hybrid-lab/PyOpticL_Rubidium_System/Production/Repumper_consolidated/Repumper_consolidated2.png

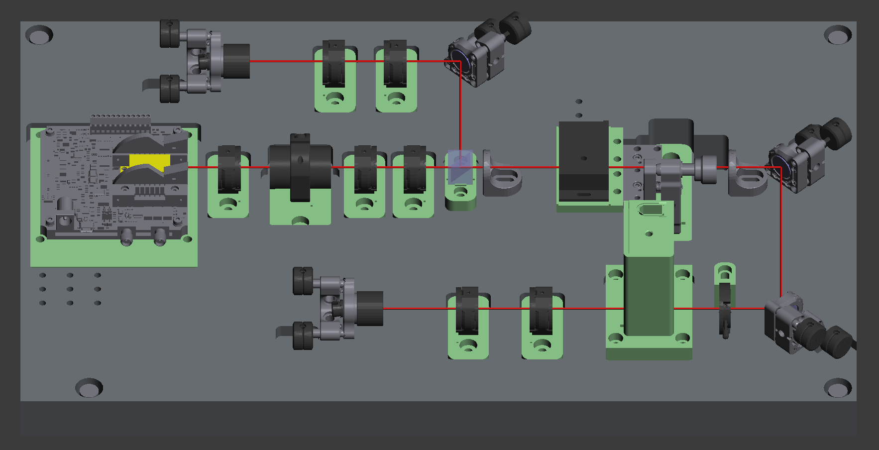
Production/Repumper_consolidated/Repumper_consolidated2.png
