hybrid-lab/PyOpticL_Rubidium_System/Rubidium_system/3DModel/StepFiles_unsorted/IsolatorSurfaceAdaptor.step

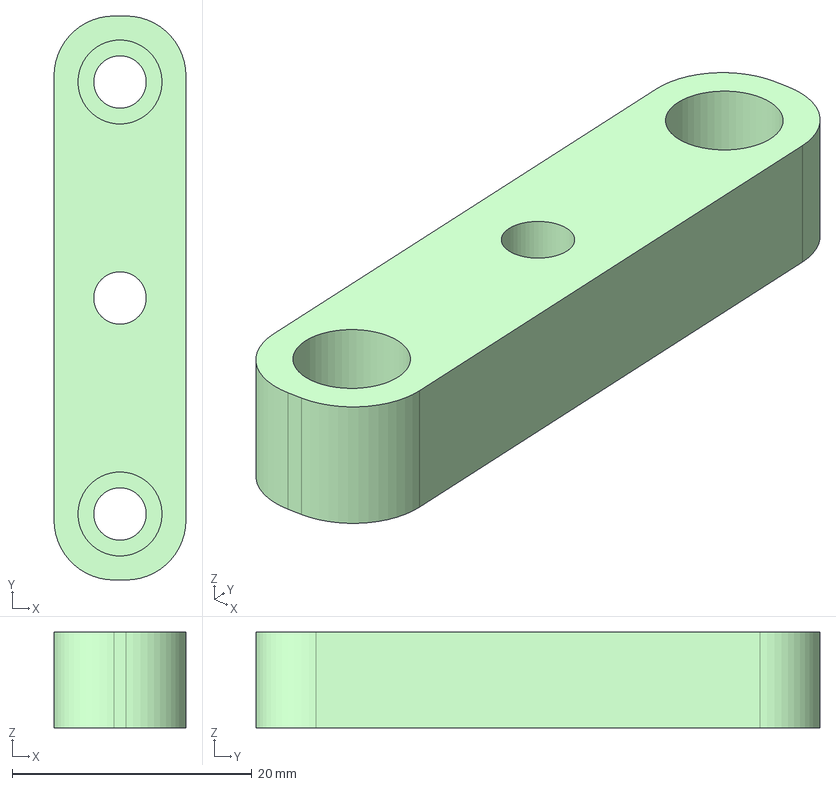
[picture p30: CAD file, 2025-08-15]
Rubidium_system/3DModel/StepFiles_unsorted/IsolatorSurfaceAdaptor.step
11.0 x 47.0 x 8.00 mm
