hybrid-lab/PyOpticL_Rubidium_System/stl/JosiahExportedSTLs/eyP-BFW01-171218.stl

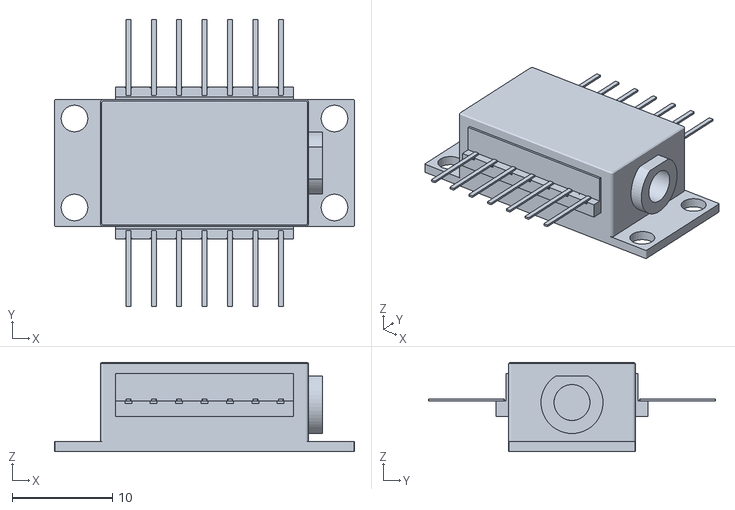
[picture p31: CAD file, 2025-08-15]
stl/JosiahExportedSTLs/eyP-BFW01-171218.stl
30.0 x 28.7 x 8.90
