hybrid-lab/PyOpticL_Rubidium_System/stl/KA05A.stl

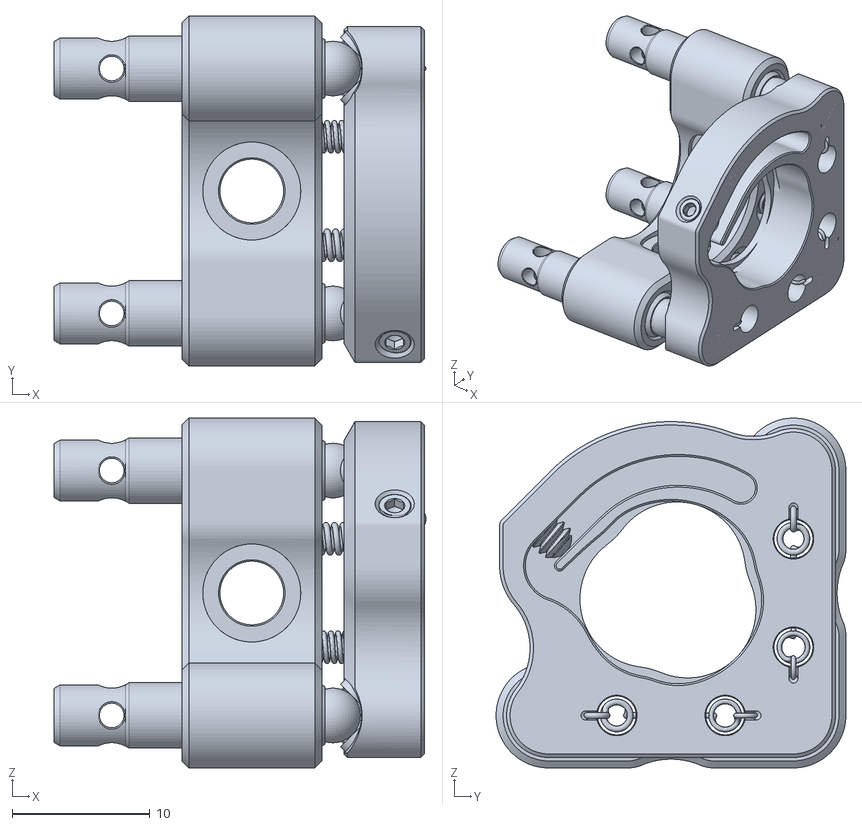
[picture p32: CAD file, 2026-06-10]
stl/KA05A.stl
27.0 x 25.4 x 25.4
