hybrid-lab/PyOpticL_Rubidium_System/stl/Shared-PyOpticL-Folder/POLARIS-B1G-Step.stl

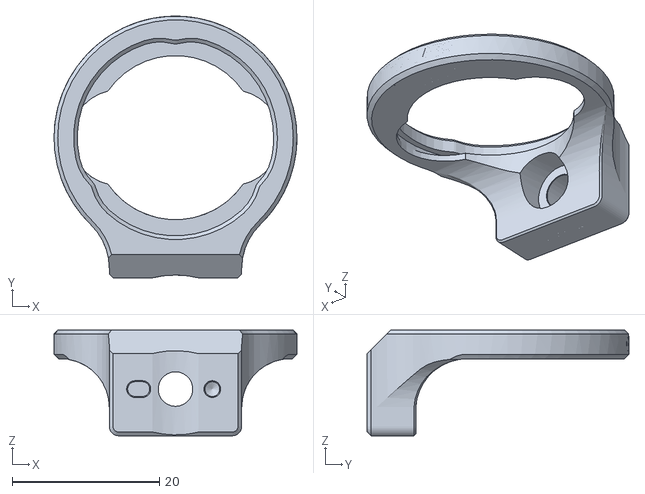
[picture p33: CAD file, 2025-08-15]
stl/Shared-PyOpticL-Folder/POLARIS-B1G-Step.stl
33.0 x 35.6 x 14.3
