hybrid-lab/PyOpticL_Rubidium_System/Adapters/Rb_Cell_2.stl

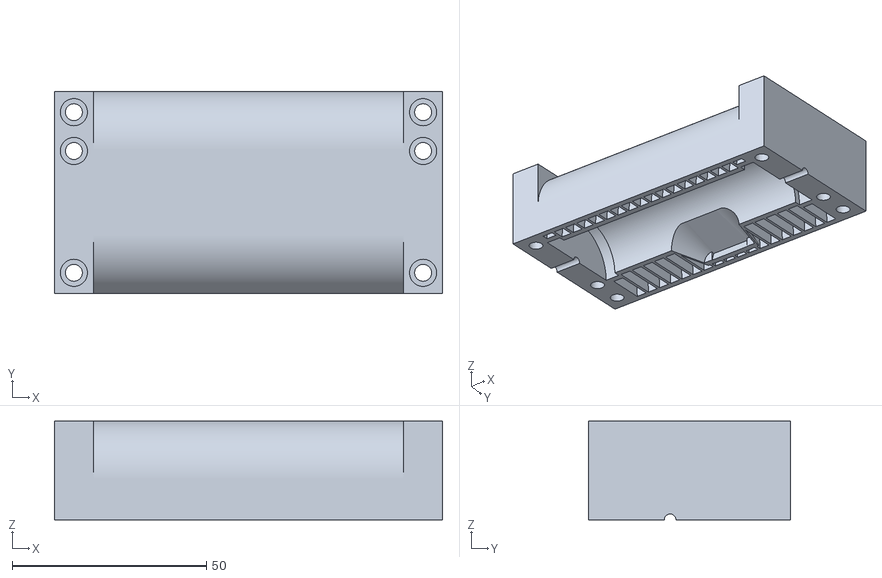
[picture p34: CAD file, 2025-08-15]
Adapters/Rb_Cell_2.stl
100.0 x 52.0 x 25.4
