hybrid-lab/PyOpticL_Rubidium_System/Oriented Step Files/KA05D.step

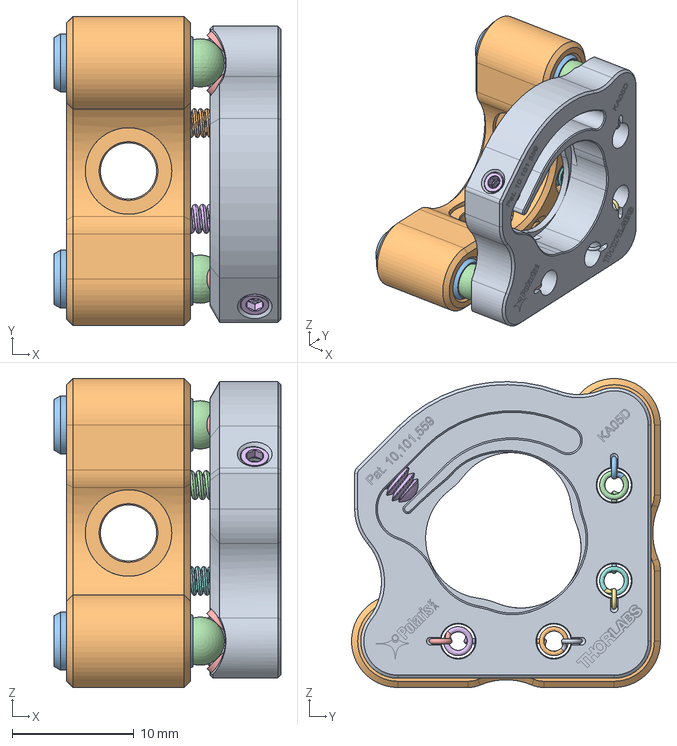
[picture p35: CAD file, 2026-06-10]
Oriented Step Files/KA05D.step
18.6 x 25.4 x 25.4 mm
