hybrid-lab/PyOpticL_Rubidium_System/Production/Adapters/Cube_Mount_Halfinch_2taps.step

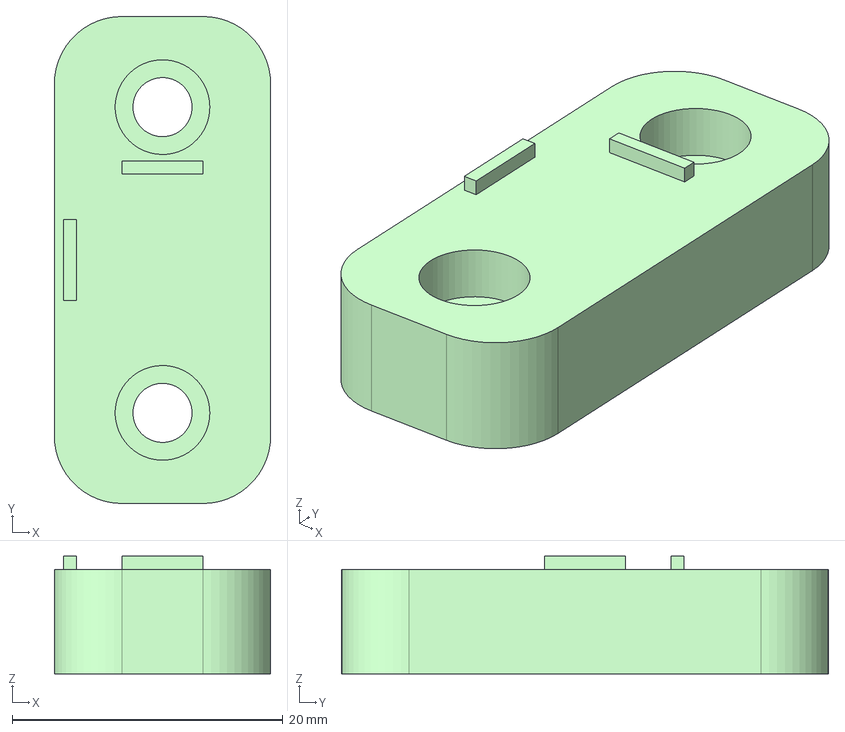
[picture p36: CAD file, 2026-06-10]
Production/Adapters/Cube_Mount_Halfinch_2taps.step
16.0 x 36.0 x 8.70 mm
