hybrid-lab/PyOpticL_Rubidium_System/Production/Adapters/Stepfile/Shutter_Adapter.step

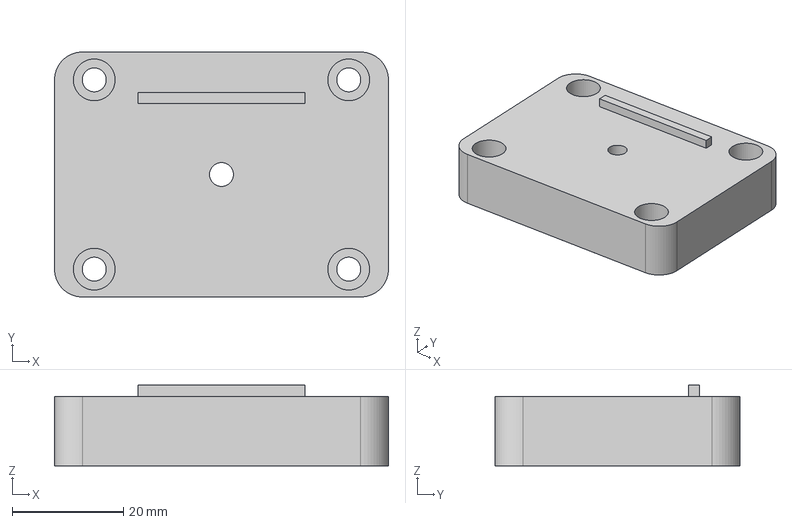
[picture p37: CAD file, 2026-06-10]
Production/Adapters/Stepfile/Shutter_Adapter.step
60.0 x 44.0 x 14.5 mm
