hybrid-lab/PyOpticL_Rubidium_System/Production/AOM_Singlepass/Step Files/FMP05_Adapter.step

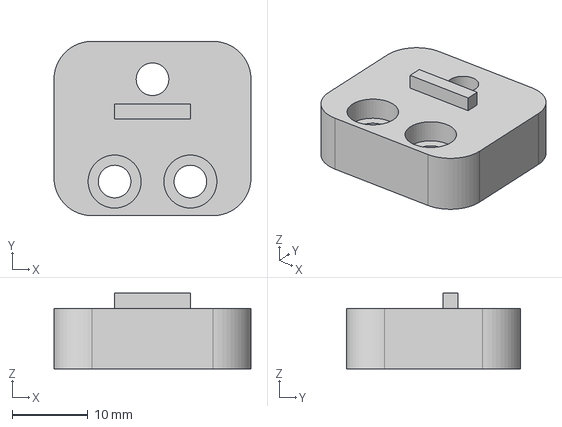
[picture p38: CAD file, 2025-12-15]
Production/AOM_Singlepass/Step Files/FMP05_Adapter.step
26.0 x 23.0 x 10.0 mm
