hybrid-lab/PyOpticL_Rubidium_System/Production/AOMBoard/StepFile/AOM_Baseplate.step

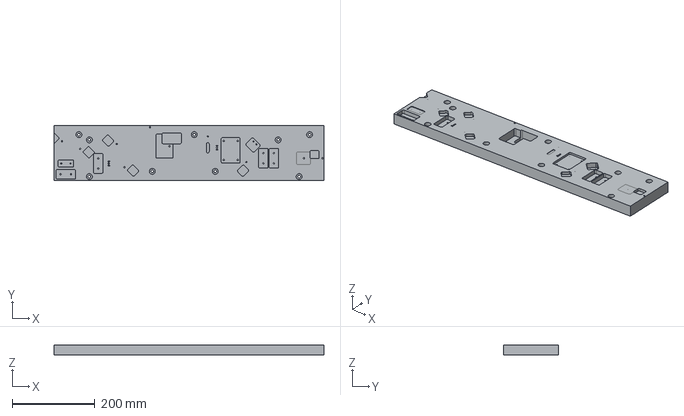
[picture p39: CAD file, 2025-12-15]
Production/AOMBoard/StepFile/AOM_Baseplate.step
654.1 x 133.3 x 25.4 mm
