hybrid-lab/PyOpticL_Rubidium_System/Production/LaserBoard2/StepFile/IPS_adapter.step

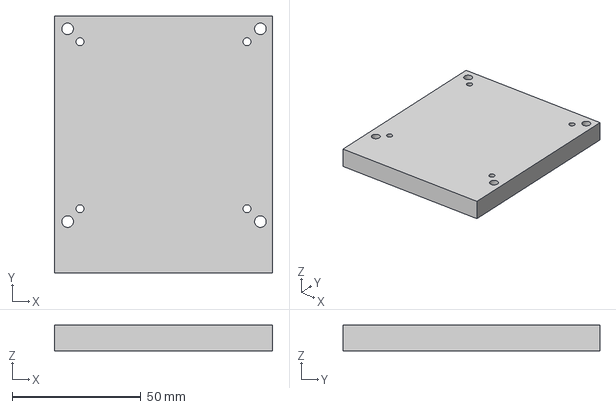
[picture p40: CAD file, 2025-12-15]
Production/LaserBoard2/StepFile/IPS_adapter.step
85.0 x 100.0 x 10.0 mm
