hybrid-lab/PyOpticL_Rubidium_System/Production/TABoard/Stepfile/TA_adapter.step

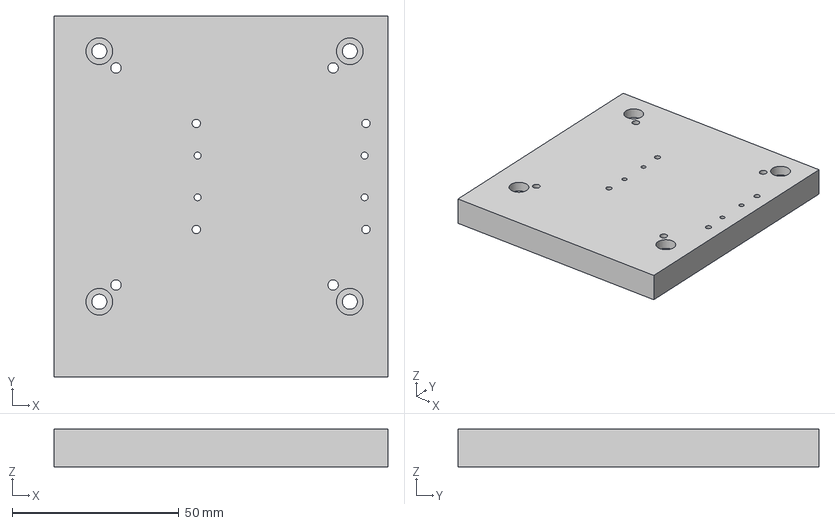
[picture p41: CAD file, 2025-12-15]
Production/TABoard/Stepfile/TA_adapter.step
100.0 x 108.0 x 11.3 mm
