hybrid-lab/PyOpticL_Rubidium_System/Rubidium_system/3DModel/Eagleyard/eyP-BFYxx-190108.stp

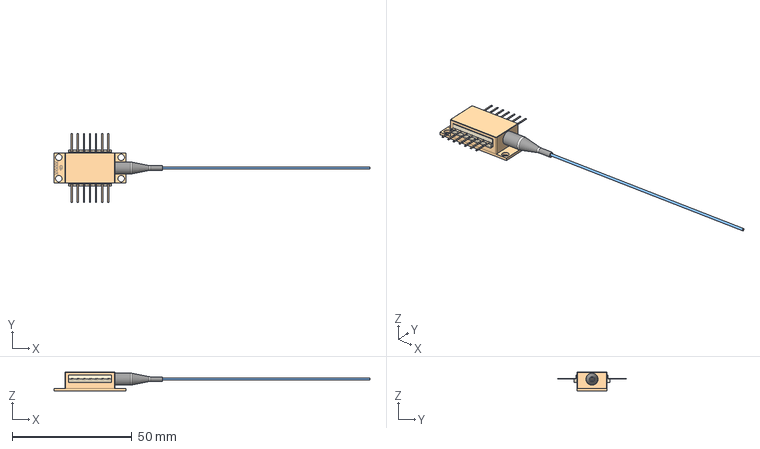
[picture p42: CAD file, 2025-08-15]
Rubidium_system/3DModel/Eagleyard/eyP-BFYxx-190108.stp
131.7 x 28.7 x 7.80 mm
