hybrid-lab/PyOpticL_Rubidium_System/Rubidium_system/3DModel/StepFiles_unsorted/GenericBase.step

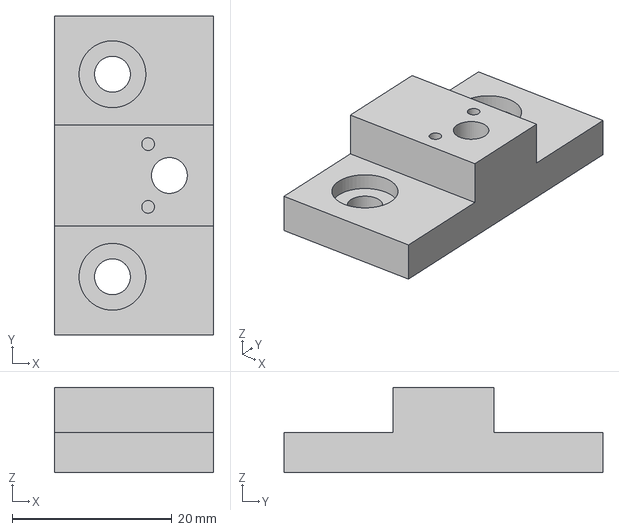
[picture p43: CAD file, 2025-08-15]
Rubidium_system/3DModel/StepFiles_unsorted/GenericBase.step
20.0 x 40.0 x 10.7 mm
