hybrid-lab/PyOpticL_Rubidium_System/stl/JosiahExportedSTLs/Koheron-CTL200-V5.stl

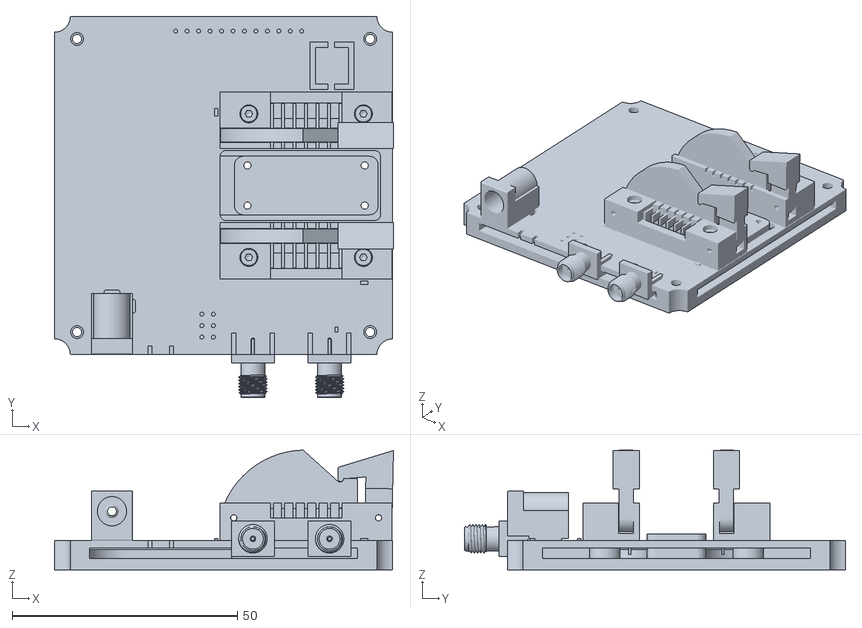
[picture p44: CAD file, 2025-08-15]
stl/JosiahExportedSTLs/Koheron-CTL200-V5.stl
75.2 x 84.5 x 26.6
