hybrid-lab/PyOpticL_Rubidium_System/stl/M05X.stl

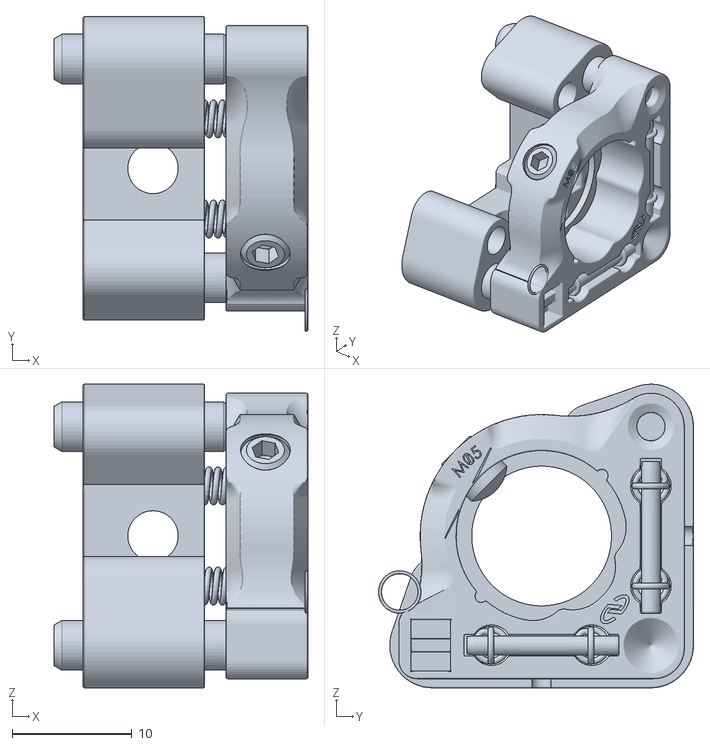
[picture p45: CAD file, 2026-06-10]
stl/M05X.stl
21.2 x 26.3 x 25.4
