hybrid-lab/PyOpticL_Rubidium_System/stl/Shared-PyOpticL-Folder/rb_cell_holder_middle.stl

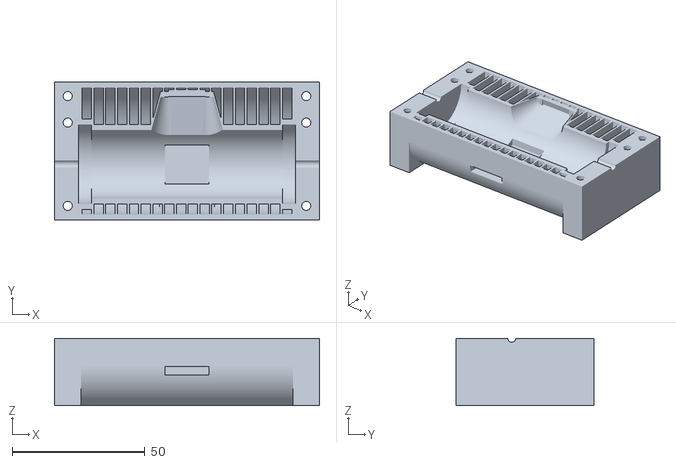
[picture p46: CAD file, 2025-08-15]
stl/Shared-PyOpticL-Folder/rb_cell_holder_middle.stl
100.0 x 52.0 x 25.4
