hybrid-lab/PyOpticL_Rubidium_System/Adapters/Surface_Adapter_FIberport_rotate_lip.step

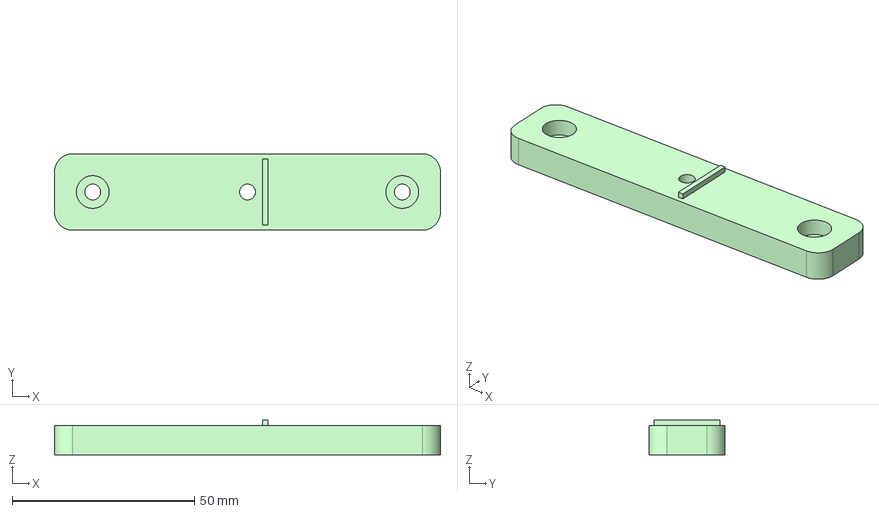
[picture p47: CAD file, 2025-08-15]
Adapters/Surface_Adapter_FIberport_rotate_lip.step
106.0 x 21.0 x 9.50 mm
