hybrid-lab/PyOpticL_Rubidium_System/Oriented Step Files/KA05A.step

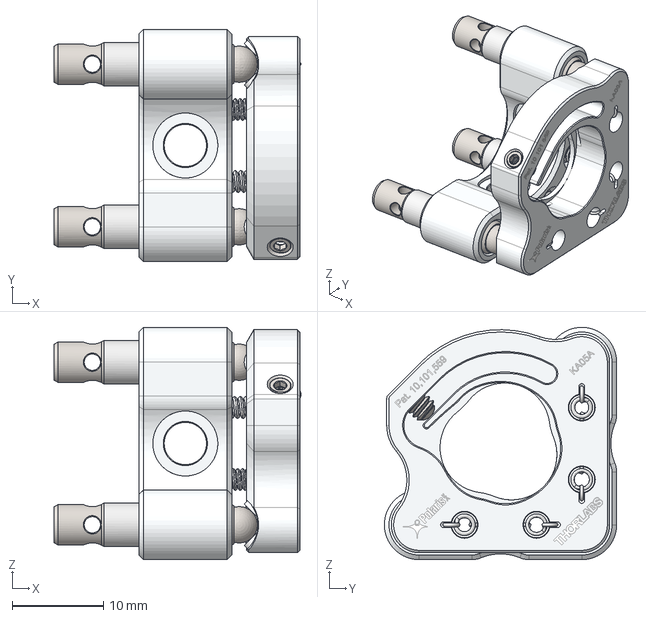
[picture p48: CAD file, 2026-06-10]
Oriented Step Files/KA05A.step
27.0 x 25.4 x 25.4 mm
