hybrid-lab/PyOpticL_Rubidium_System/Production/Adapters/Stepfile/Surface_Adapter_PD.step

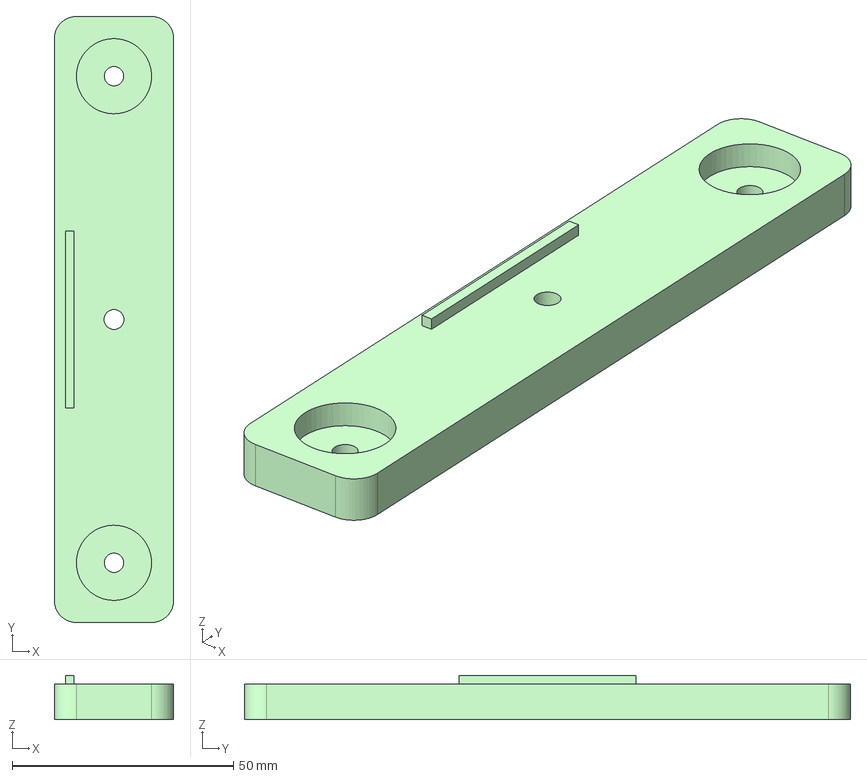
[picture p49: CAD file, 2025-12-15]
Production/Adapters/Stepfile/Surface_Adapter_PD.step
27.0 x 137.0 x 10.0 mm
