hybrid-lab/PyOpticL_Rubidium_System/Production/Adapters/Surface_Adapter_isolator_1295.step

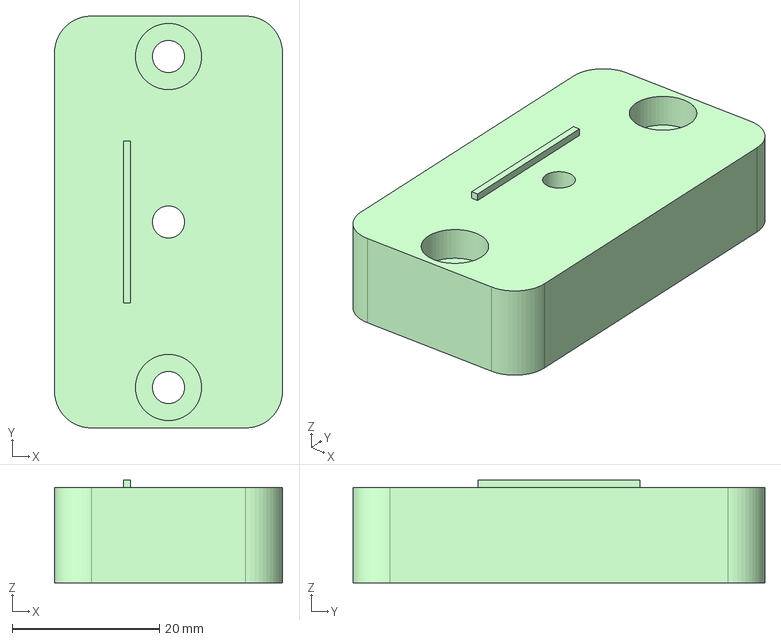
[picture p50: CAD file, 2026-06-10]
Production/Adapters/Surface_Adapter_isolator_1295.step
31.0 x 56.0 x 13.9 mm
