hybrid-lab/PyOpticL_Rubidium_System/Production/AOM_Singlepass/Step Files/Iris_Adapter.step

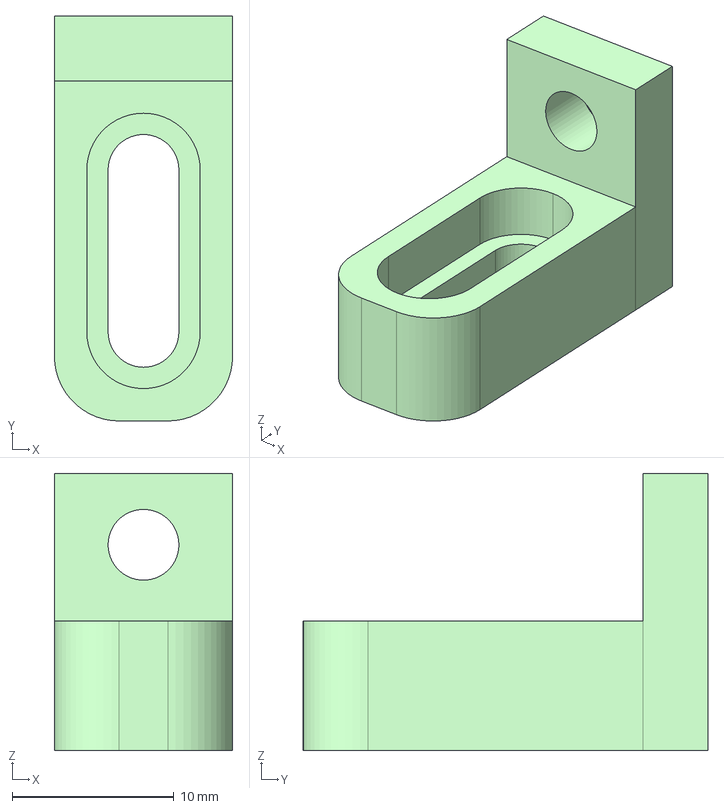
[picture p51: CAD file, 2025-08-15]
Production/AOM_Singlepass/Step Files/Iris_Adapter.step
11.0 x 25.0 x 17.1 mm
