hybrid-lab/PyOpticL_Rubidium_System/Rubidium_system/3DModel/StepFiles_unsorted/RotationMountSurfaceAdaptor.step

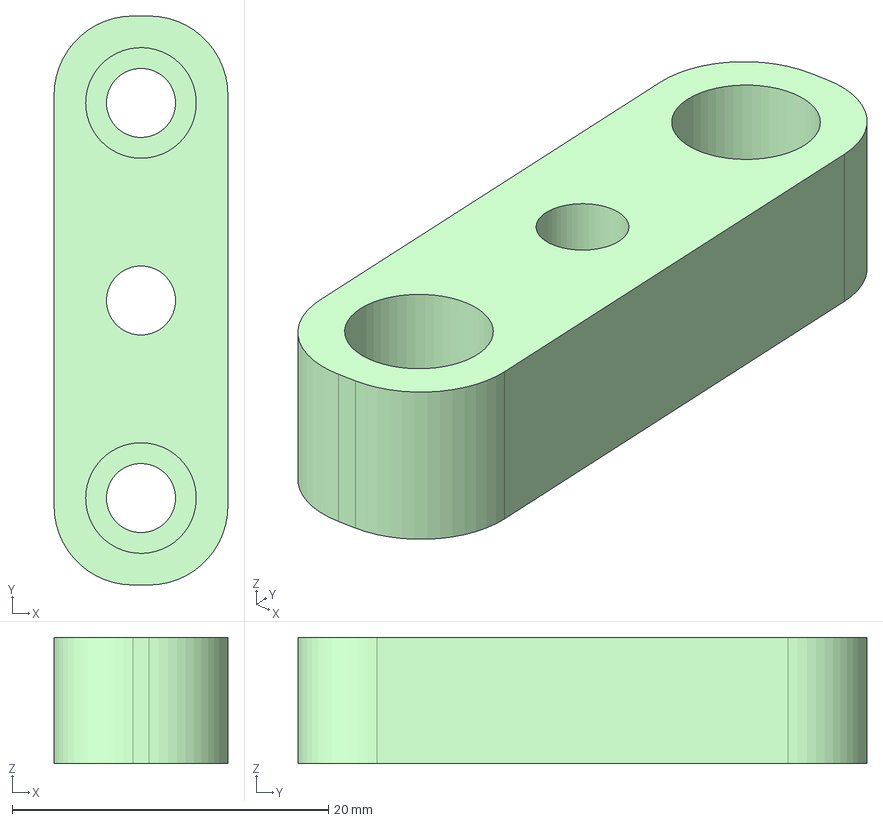
[picture p52: CAD file, 2025-08-15]
Rubidium_system/3DModel/StepFiles_unsorted/RotationMountSurfaceAdaptor.step
11.0 x 36.0 x 8.00 mm
