hybrid-lab/PyOpticL_Rubidium_System/stl/Shared-PyOpticL-Folder/HCA3-Step.stl

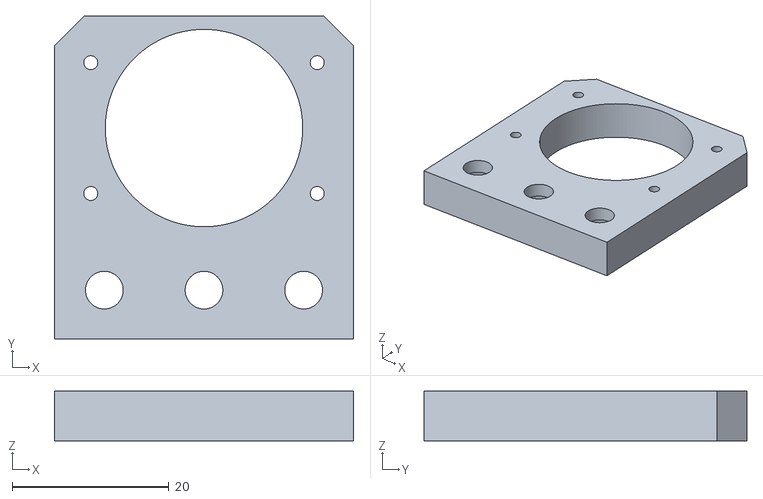
[picture p53: CAD file, 2025-08-15]
stl/Shared-PyOpticL-Folder/HCA3-Step.stl
38.1 x 41.1 x 6.35
