hybrid-lab/PyOpticL_Rubidium_System/Adapters/shutter_adapter.step

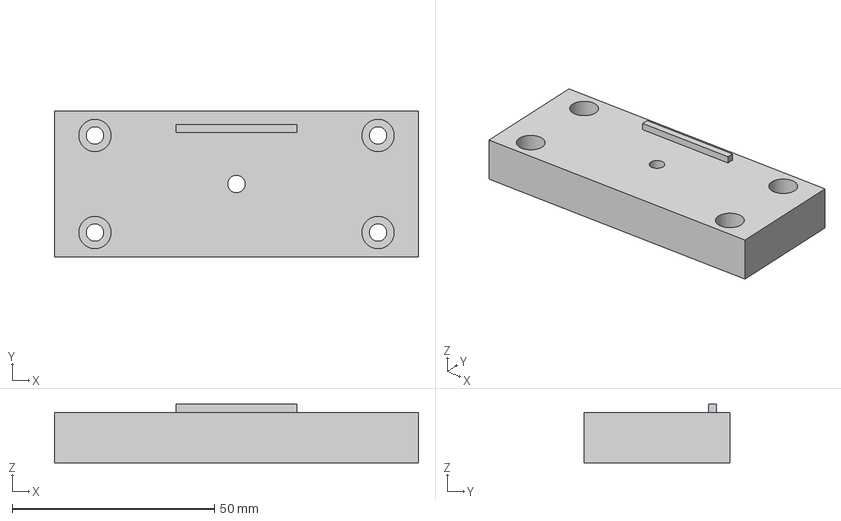
[picture p54: CAD file, 2025-08-15]
Adapters/shutter_adapter.step
90.0 x 36.0 x 14.5 mm
