hybrid-lab/PyOpticL_Rubidium_System/Oriented Step Files/MRA12-E03.step

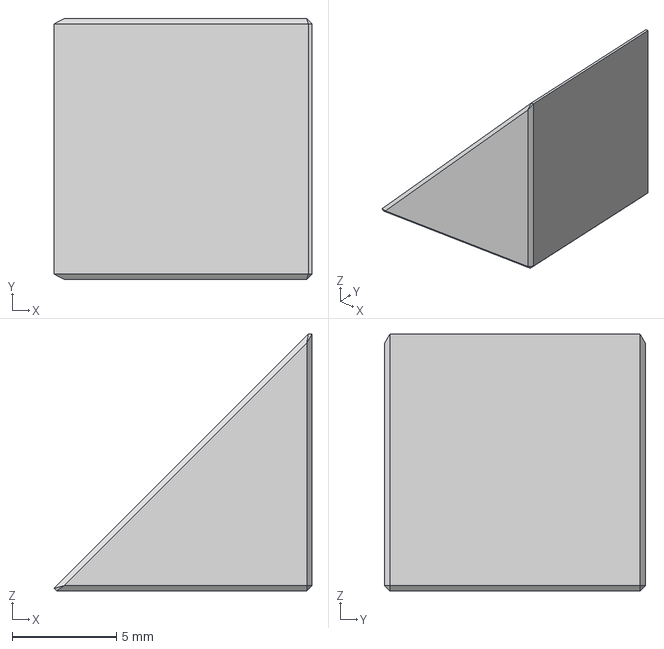
[picture p55: CAD file, 2026-06-10]
Oriented Step Files/MRA12-E03.step
12.4 x 12.5 x 12.3 mm
