hybrid-lab/PyOpticL_Rubidium_System/Production/Adapters/Aligning_Mount.step

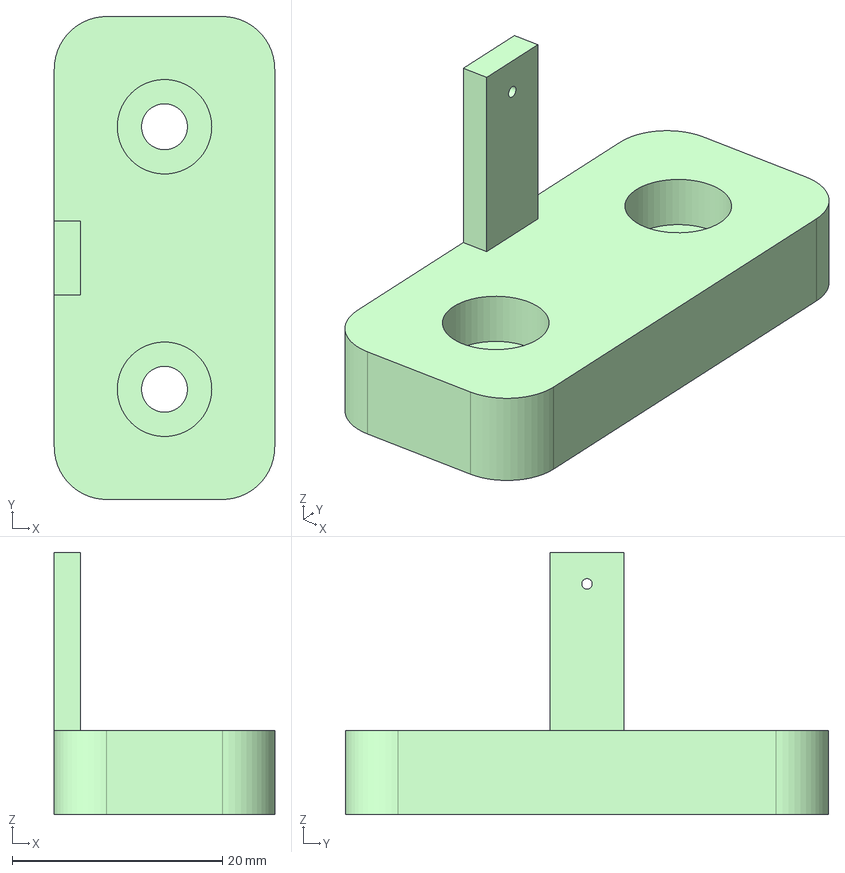
[picture p56: CAD file, 2026-06-10]
Production/Adapters/Aligning_Mount.step
21.0 x 46.0 x 25.0 mm
