hybrid-lab/PyOpticL_Rubidium_System/Production/AOM_Singlepass/Step Files/Surface_Adapter_rsp05_lip.step

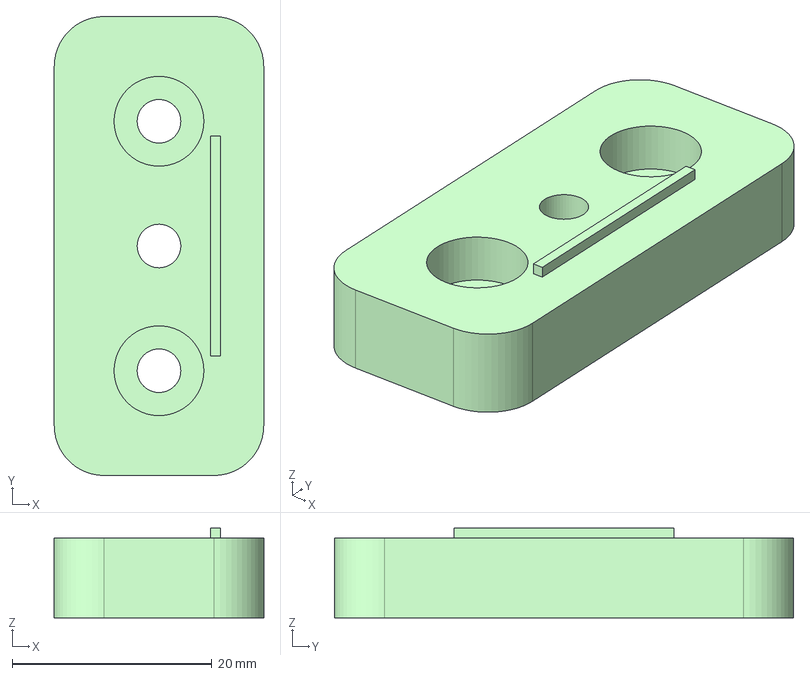
[picture p57: CAD file, 2025-08-15]
Production/AOM_Singlepass/Step Files/Surface_Adapter_rsp05_lip.step
21.0 x 46.0 x 9.00 mm
