hybrid-lab/PyOpticL_Rubidium_System/Rubidium_system/3DModel/StepFiles_unsorted/MOT_baseplate.step

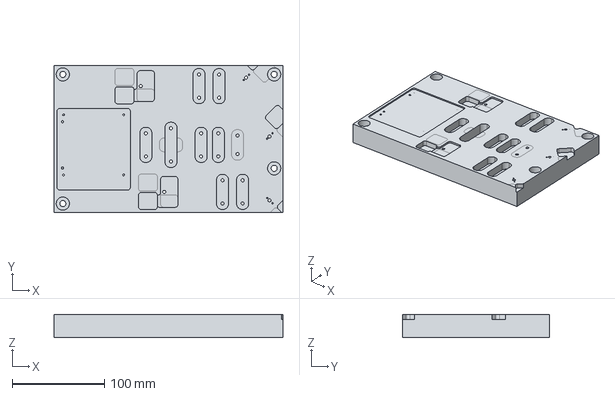
[picture p58: CAD file, 2025-08-15]
Rubidium_system/3DModel/StepFiles_unsorted/MOT_baseplate.step
247.6 x 158.8 x 25.4 mm
