hybrid-lab/PyOpticL_Rubidium_System/stl/Shared-PyOpticL-Folder/SM1L03-Step.stl

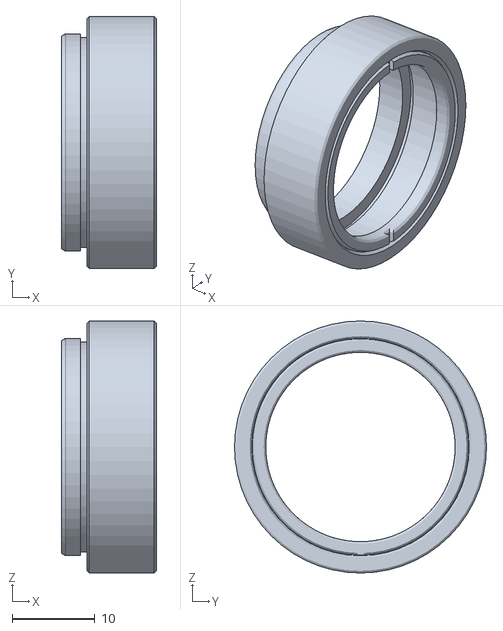
[picture p59: CAD file, 2025-08-15]
stl/Shared-PyOpticL-Folder/SM1L03-Step.stl
11.4 x 30.5 x 30.5
