hybrid-lab/PyOpticL_Rubidium_System/Production/Adapters/Stepfile/Laser_board_adapter.step

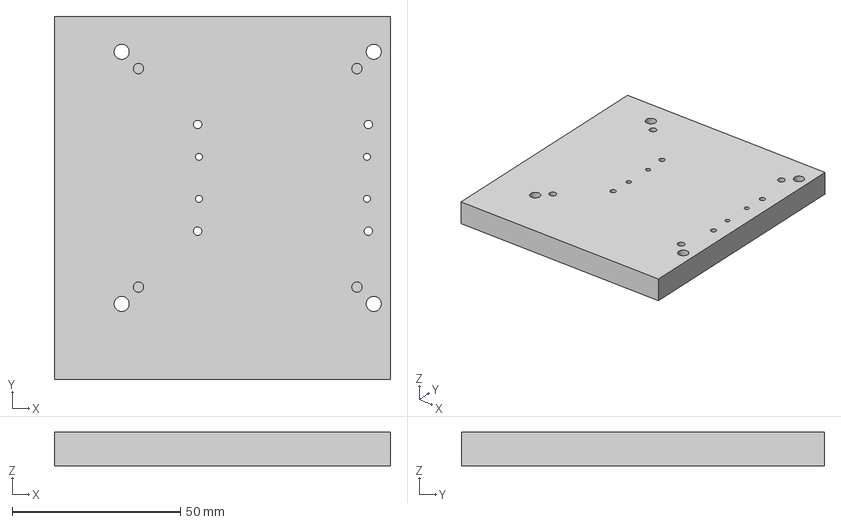
[picture p60: CAD file, 2025-12-15]
Production/Adapters/Stepfile/Laser_board_adapter.step
100.0 x 108.0 x 10.0 mm
