hybrid-lab/PyOpticL_Rubidium_System/Production/TABoard/Stepfile/Surface_Adapter_isolator_lip.step

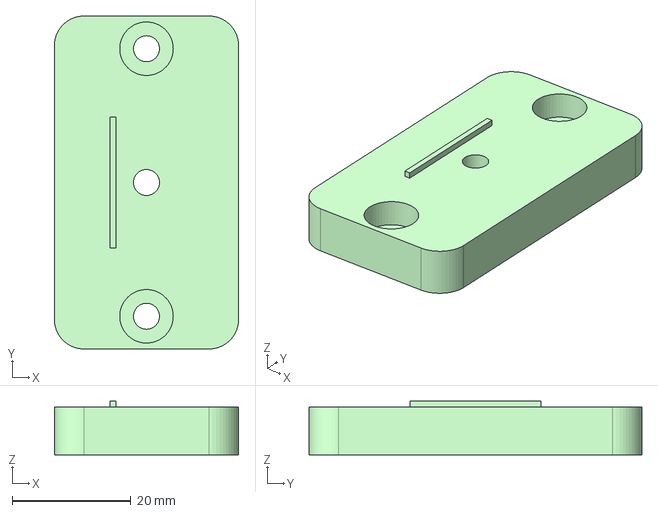
[picture p61: CAD file, 2025-08-15]
Production/TABoard/Stepfile/Surface_Adapter_isolator_lip.step
31.0 x 56.0 x 9.00 mm
