hybrid-lab/PyOpticL_Rubidium_System/Rubidium_system/3DModel/StepFiles_unsorted/POLARIS-K05S1-Solidworks.sldprt

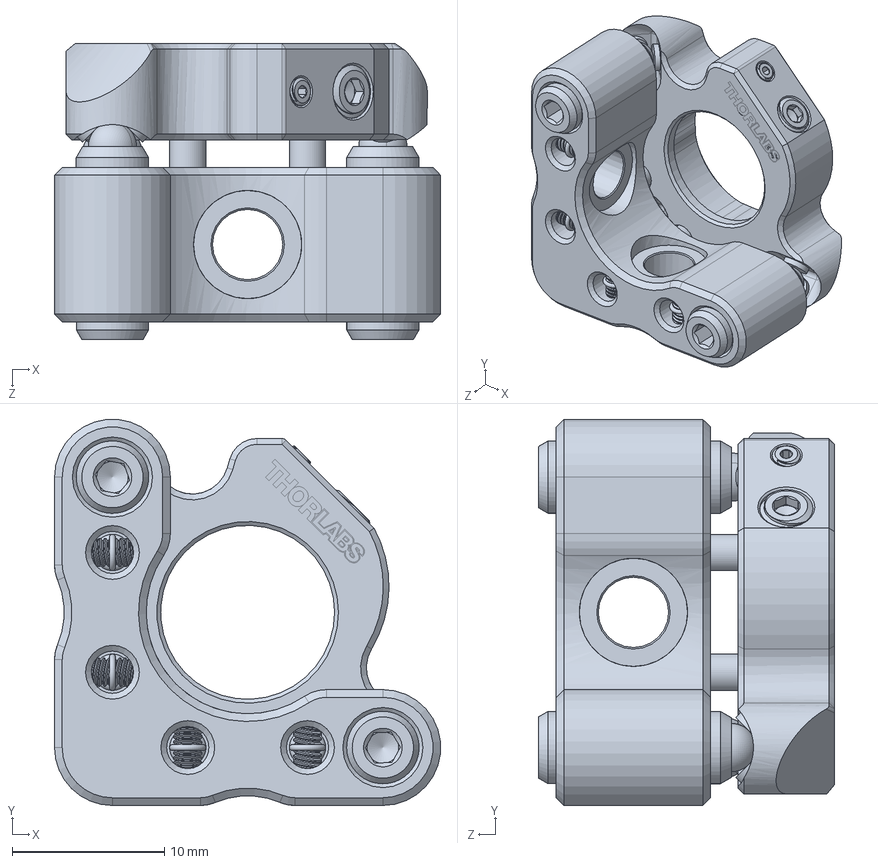
[picture p62: CAD file, 2025-08-15]
Rubidium_system/3DModel/StepFiles_unsorted/POLARIS-K05S1-Solidworks.sldprt
25.4 x 25.4 x 19.5 mm
