hybrid-lab/PyOpticL_Rubidium_System/Adapters/Cube_Mount.step

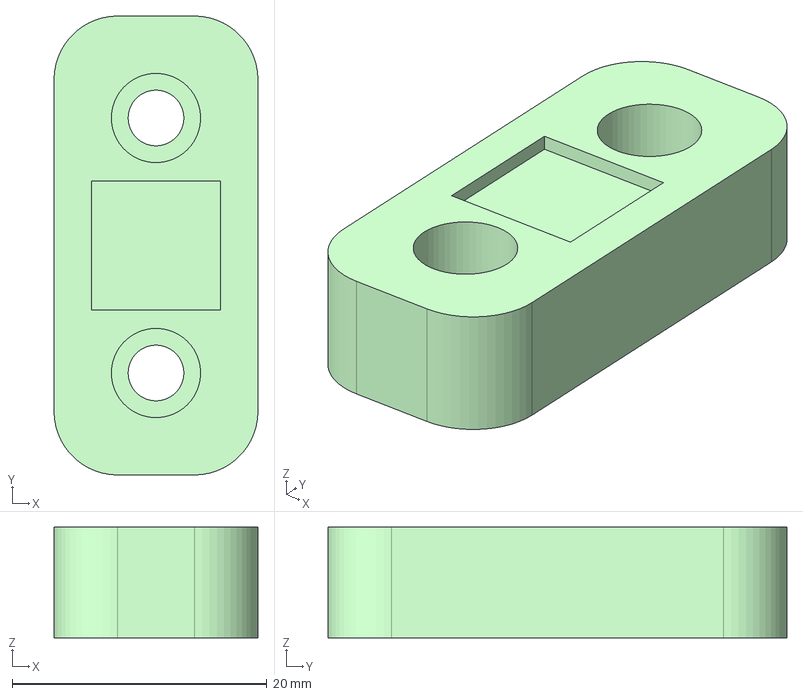
[picture p63: CAD file, 2025-08-15]
Adapters/Cube_Mount.step
16.0 x 36.0 x 8.70 mm
