hybrid-lab/PyOpticL_Rubidium_System/Oriented Step Files/KA05T.step

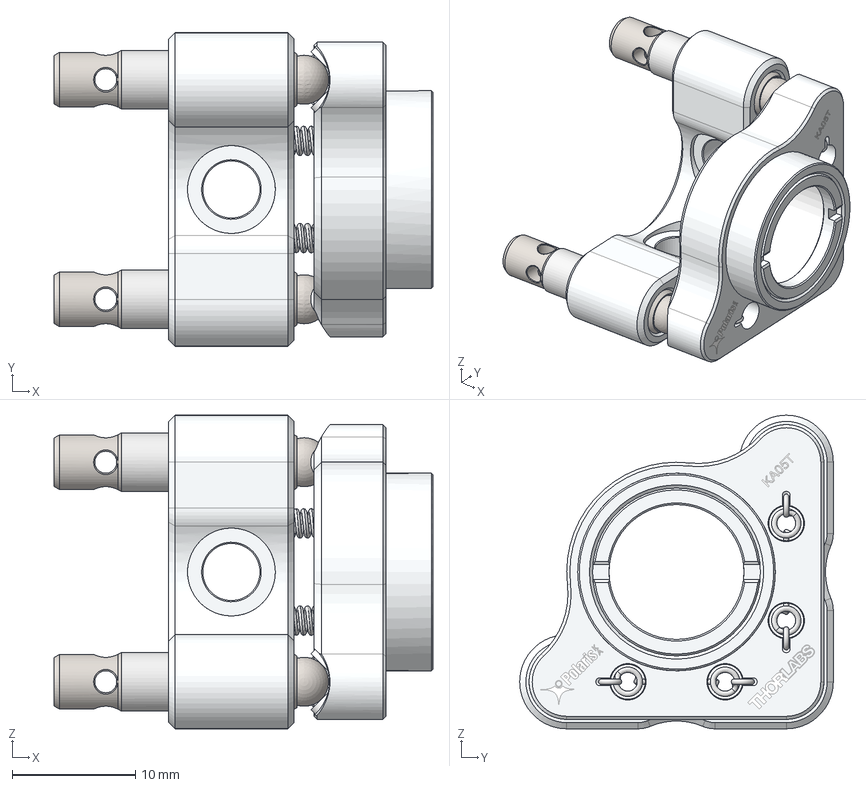
[picture p64: CAD file, 2025-11-09]
Oriented Step Files/KA05T.step
30.7 x 25.4 x 25.4 mm
