hybrid-lab/PyOpticL_Rubidium_System/Production/Adapters/Rightangle_mirror_mount.step

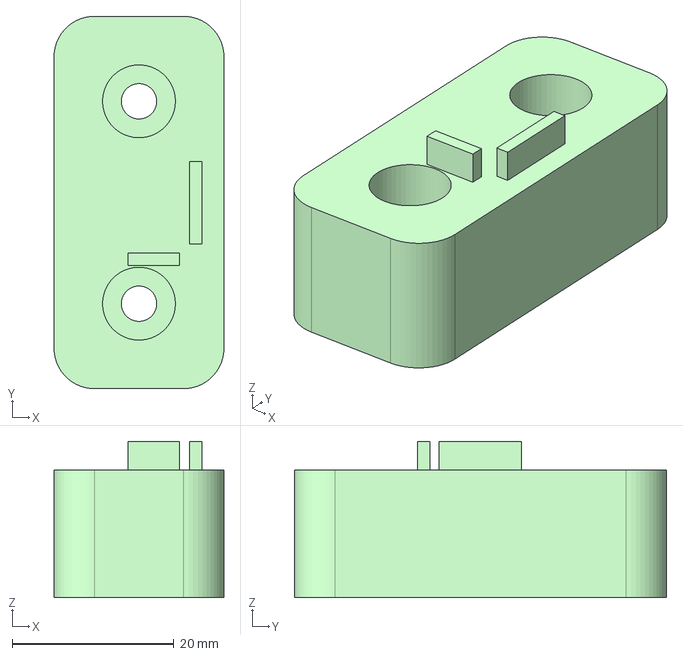
[picture p65: CAD file, 2026-06-10]
Production/Adapters/Rightangle_mirror_mount.step
21.0 x 46.0 x 19.3 mm
