hybrid-lab/PyOpticL_Rubidium_System/Rubidium_system/3DModel/StepFiles_unsorted/Repump-Baseplate.step

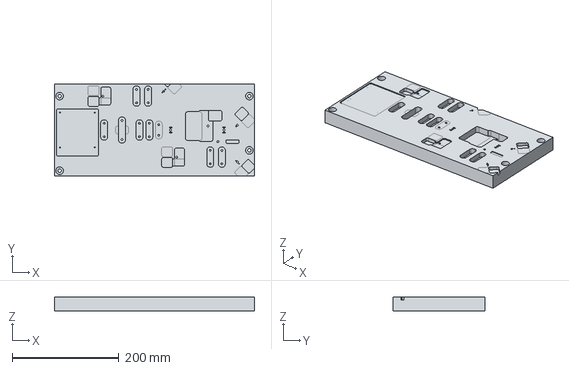
[picture p66: CAD file, 2025-08-15]
Rubidium_system/3DModel/StepFiles_unsorted/Repump-Baseplate.step
374.6 x 171.4 x 25.4 mm
