hybrid-lab/PyOpticL_Rubidium_System/stl/Fiber_Clamp_3_top1.stl

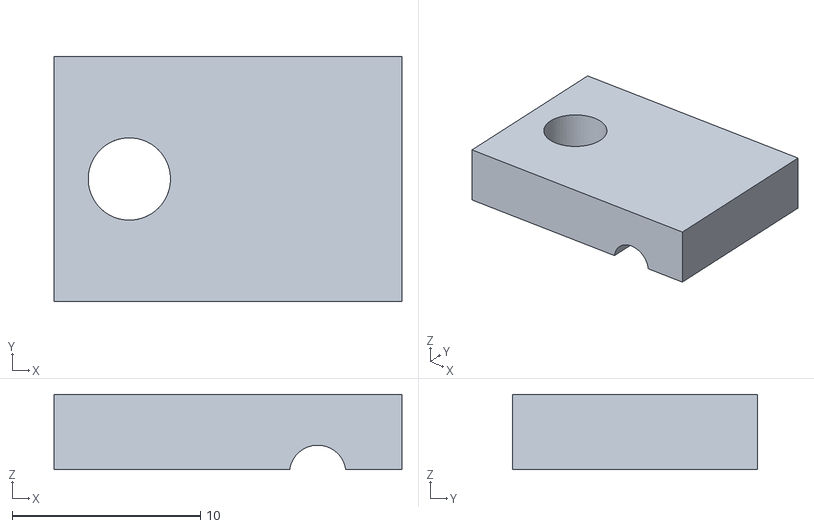
[picture p67: CAD file, 2026-06-10]
stl/Fiber_Clamp_3_top1.stl
18.5 x 13.0 x 4.00
