hybrid-lab/PyOpticL_Rubidium_System/stl/Shared-PyOpticL-Folder/KMSS_MH12_step.stl

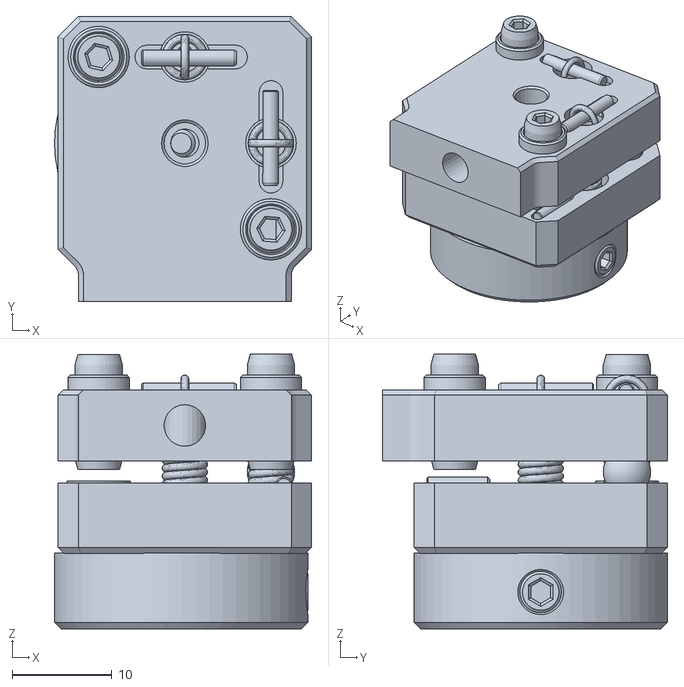
[picture p68: CAD file, 2025-08-15]
stl/Shared-PyOpticL-Folder/KMSS_MH12_step.stl
25.8 x 28.6 x 27.5
