hybrid-lab/PyOpticL_Rubidium_System/Oriented Step Files/IPS_laser.step

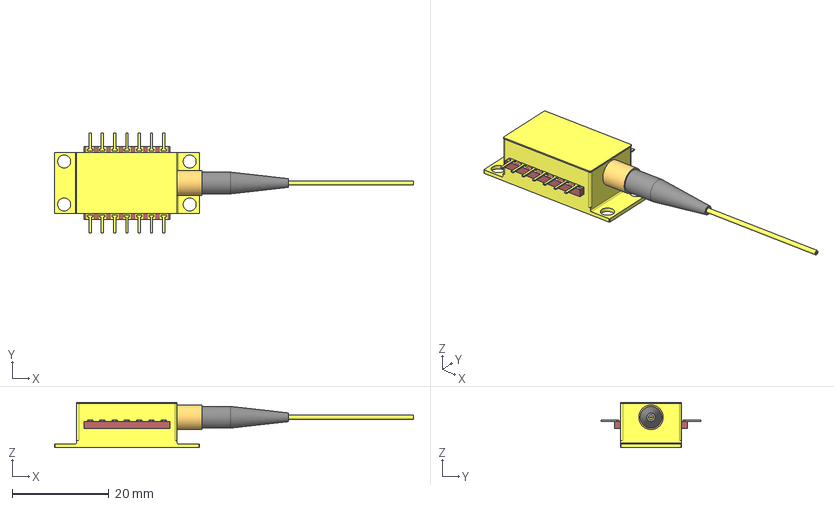
[picture p69: CAD file, 2025-11-09]
Oriented Step Files/IPS_laser.step
74.4 x 20.7 x 9.39 mm
