hybrid-lab/PyOpticL_Rubidium_System/Production/Baseplate/SAS_Baseplate.step

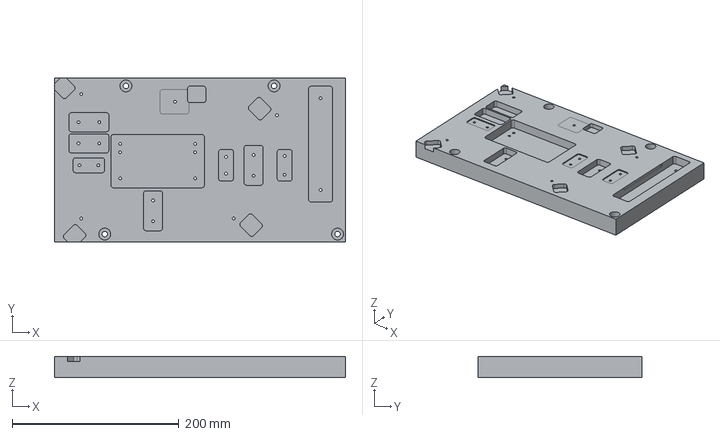
[picture p70: CAD file, 2025-11-09]
Production/Baseplate/SAS_Baseplate.step
349.2 x 196.8 x 25.4 mm
