hybrid-lab/PyOpticL_Rubidium_System/Rubidium_system/3DModel/StepFiles_unsorted/PBSSurfaceAdaptor.step

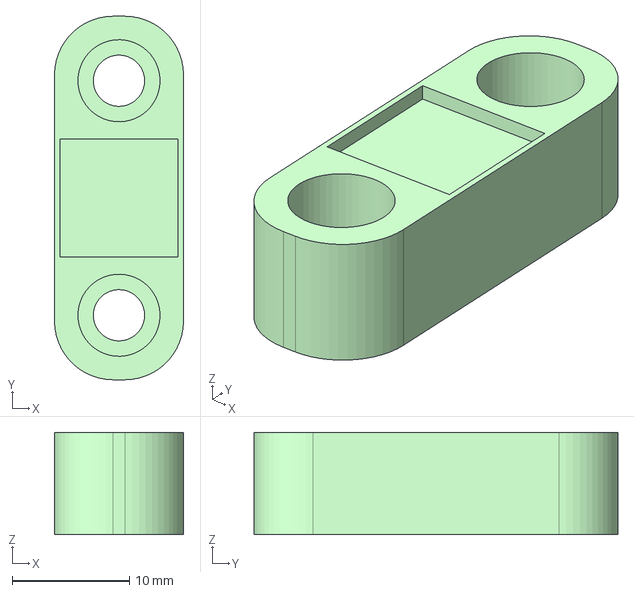
[picture p71: CAD file, 2025-08-15]
Rubidium_system/3DModel/StepFiles_unsorted/PBSSurfaceAdaptor.step
11.0 x 31.0 x 8.70 mm
