hybrid-lab/PyOpticL_Rubidium_System/stl/Shared-PyOpticL-Folder/S05TM09-Step.stl

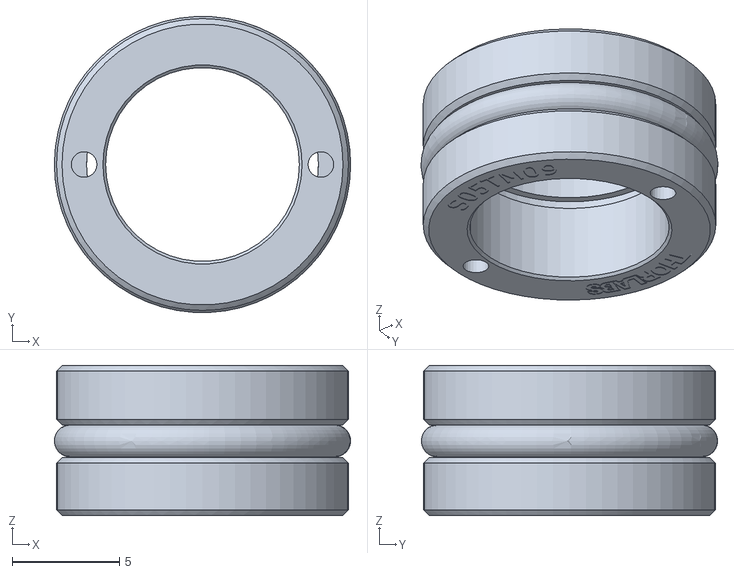
[picture p72: CAD file, 2025-08-15]
stl/Shared-PyOpticL-Folder/S05TM09-Step.stl
13.8 x 13.8 x 6.99
