hybrid-lab/PyOpticL_Rubidium_System/Adapters/PD_Mount.step

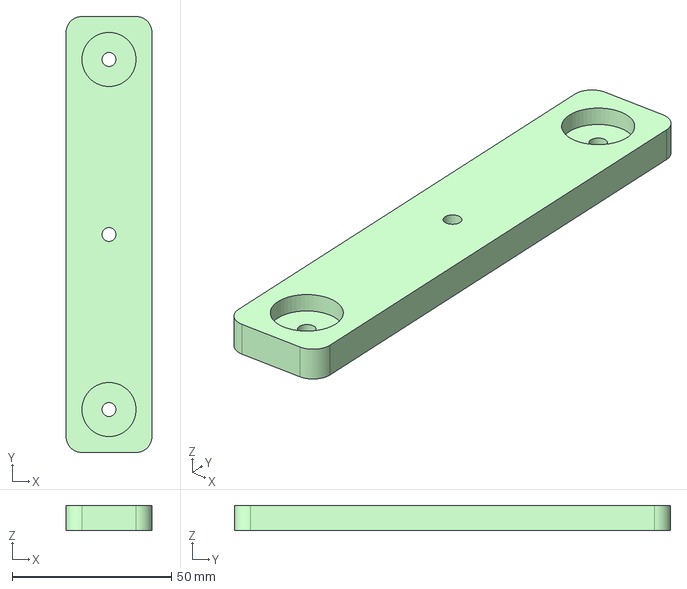
[picture p73: CAD file, 2025-08-15]
Adapters/PD_Mount.step
27.0 x 137.0 x 8.00 mm
