hybrid-lab/PyOpticL_Rubidium_System/stl/KA05D.stl

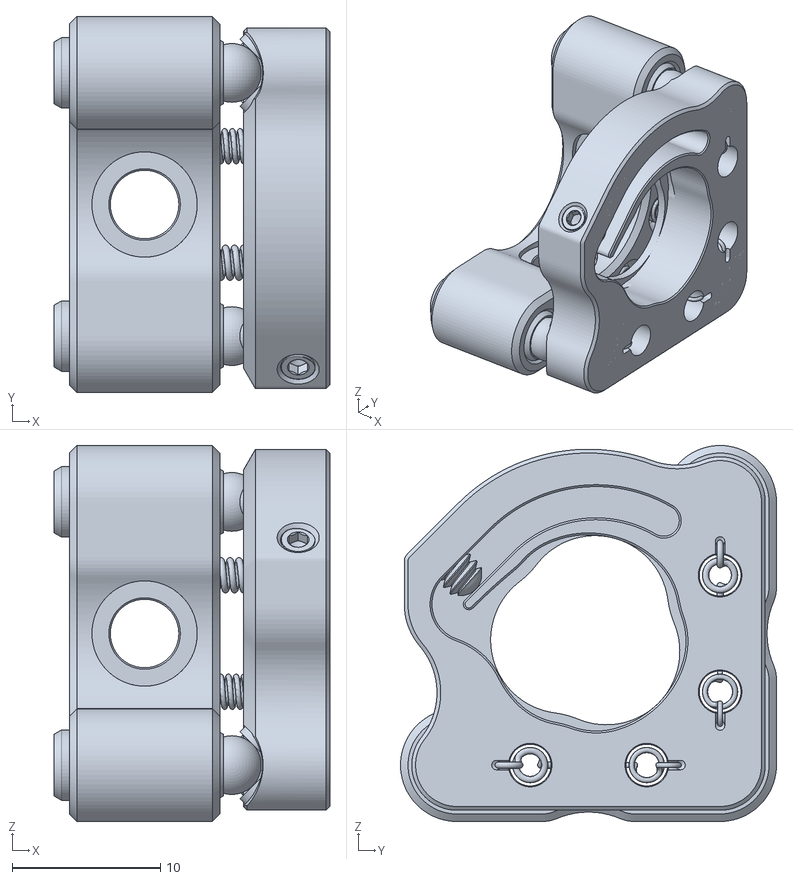
[picture p74: CAD file, 2026-06-10]
stl/KA05D.stl
18.6 x 25.4 x 25.4
