hybrid-lab/PyOpticL_Rubidium_System/stl/Shared-PyOpticL-Folder/POLARIS-K05S2-Step.stl

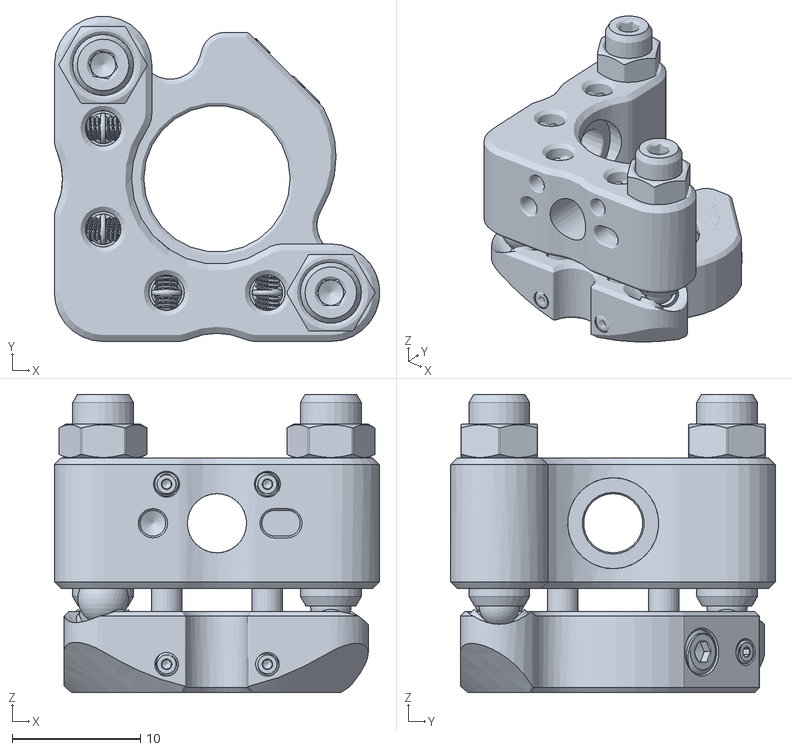
[picture p75: CAD file, 2025-08-15]
stl/Shared-PyOpticL-Folder/POLARIS-K05S2-Step.stl
25.4 x 25.4 x 23.3
