hybrid-lab/PyOpticL_Rubidium_System/Adapters/AOM_Adapter.step

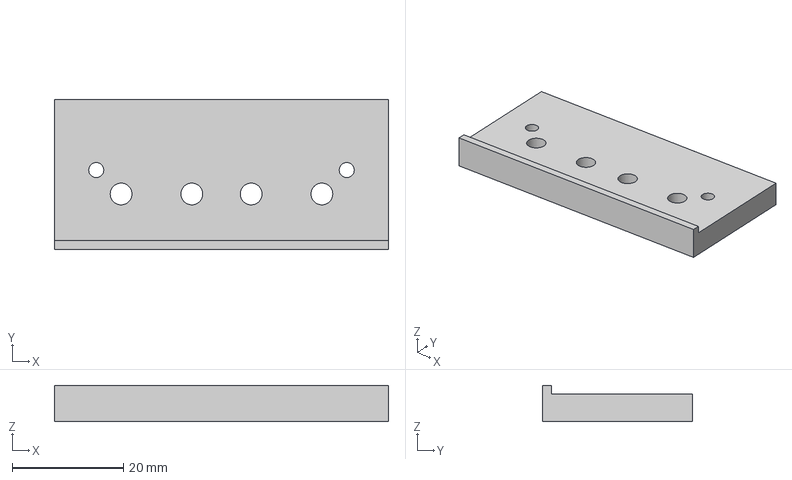
[picture p76: CAD file, 2025-08-15]
Adapters/AOM_Adapter.step
60.0 x 27.0 x 6.50 mm
