hybrid-lab/PyOpticL_Rubidium_System/Production/Adapters/Stepfile/Surface_Adapter_aom.step

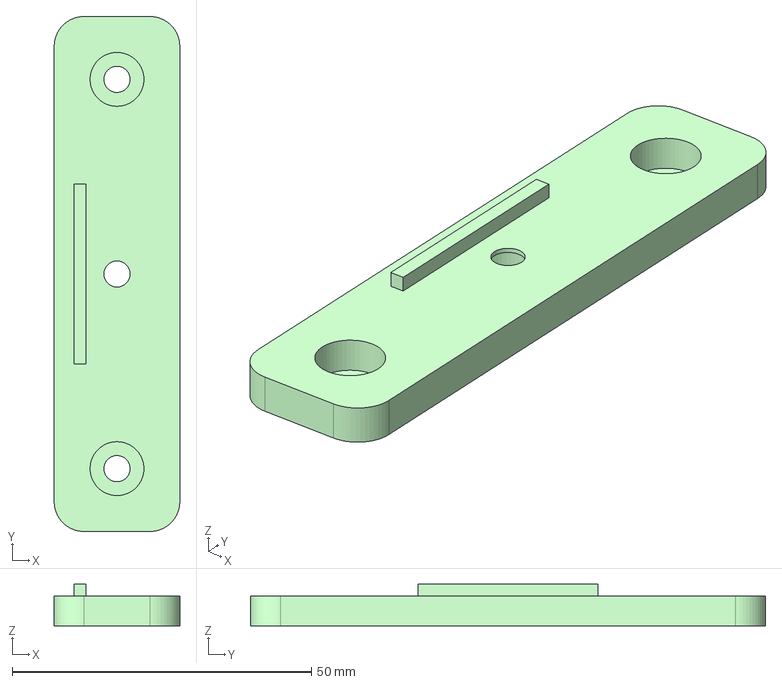
[picture p77: CAD file, 2025-08-15]
Production/Adapters/Stepfile/Surface_Adapter_aom.step
21.0 x 86.0 x 7.00 mm
