hybrid-lab/PyOpticL_Rubidium_System/stl/Fiber_Clamp_3_bottom1.stl

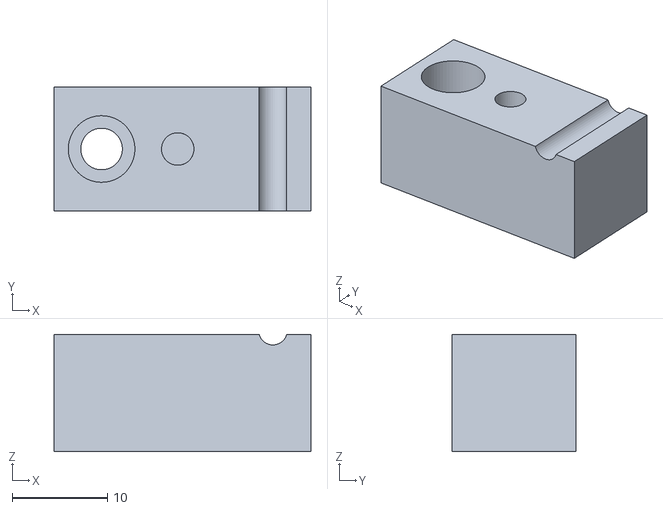
[picture p78: CAD file, 2026-06-10]
stl/Fiber_Clamp_3_bottom1.stl
27.0 x 13.0 x 12.3
