hybrid-lab/PyOpticL_Rubidium_System/stl/Shared-PyOpticL-Folder/MK05-Step.stl

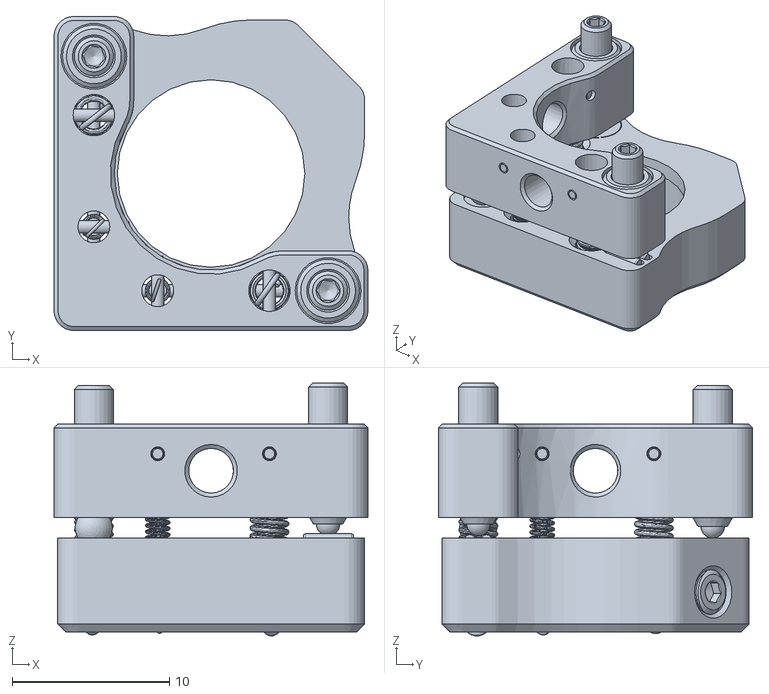
[picture p79: CAD file, 2025-08-15]
stl/Shared-PyOpticL-Folder/MK05-Step.stl
20.0 x 20.0 x 16.1
