hybrid-lab/PyOpticL_Rubidium_System/Production/Adapters/Stepfile/Surface_Adapter_fiberport_lip.step

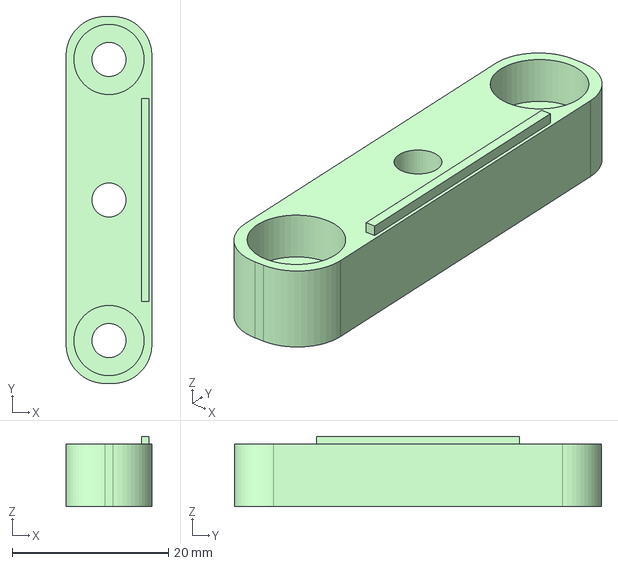
[picture p80: CAD file, 2025-08-15]
Production/Adapters/Stepfile/Surface_Adapter_fiberport_lip.step
11.0 x 47.0 x 9.00 mm
