hybrid-lab/PyOpticL_Rubidium_System/stl/Fiber_Clamp_Koheron.stl

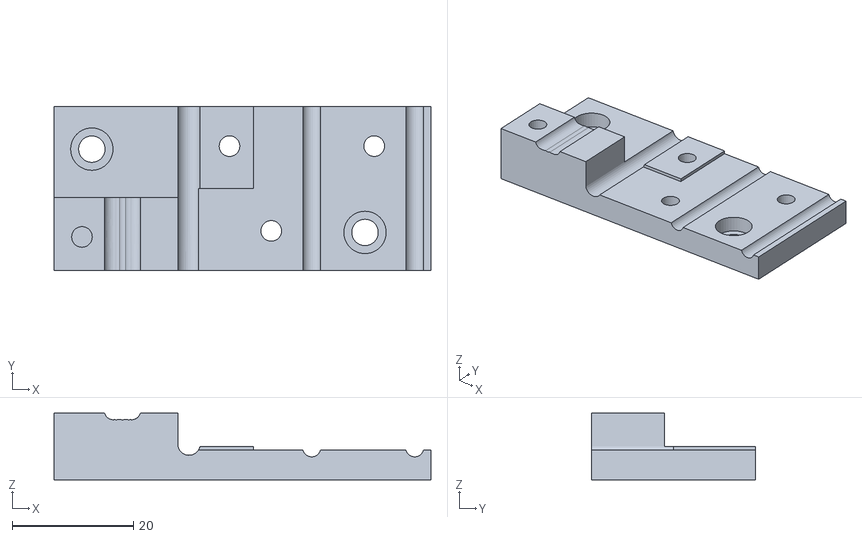
[picture p81: CAD file, 2026-06-10]
stl/Fiber_Clamp_Koheron.stl
62.2 x 27.0 x 11.0
