hybrid-lab/PyOpticL_Rubidium_System/stl/Shared-PyOpticL-Folder/C220TMD-A-Step.stl

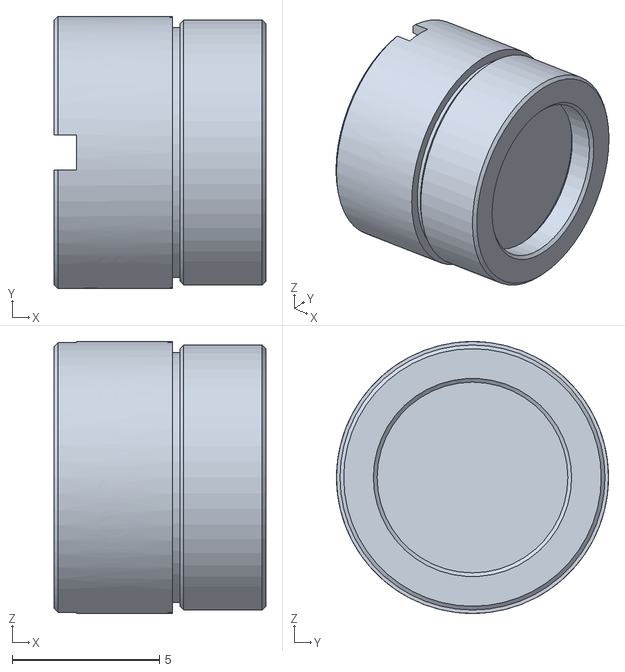
[picture p82: CAD file, 2025-08-15]
stl/Shared-PyOpticL-Folder/C220TMD-A-Step.stl
7.19 x 9.24 x 9.24
