hybrid-lab/PyOpticL_Rubidium_System/stl/Shared-PyOpticL-Folder/MK05PM-Step.stl

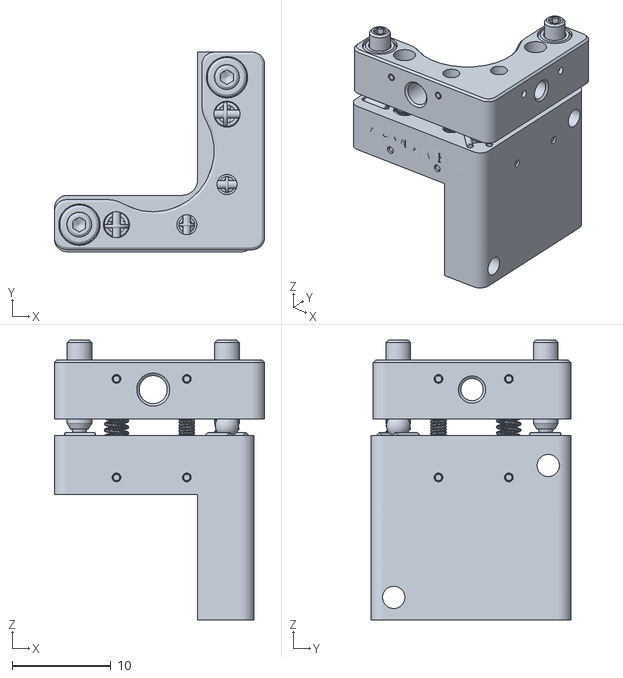
[picture p83: CAD file, 2025-08-15]
stl/Shared-PyOpticL-Folder/MK05PM-Step.stl
21.3 x 20.2 x 28.3
