hybrid-lab/PyOpticL_Rubidium_System/stl/shutter_adapter.stl

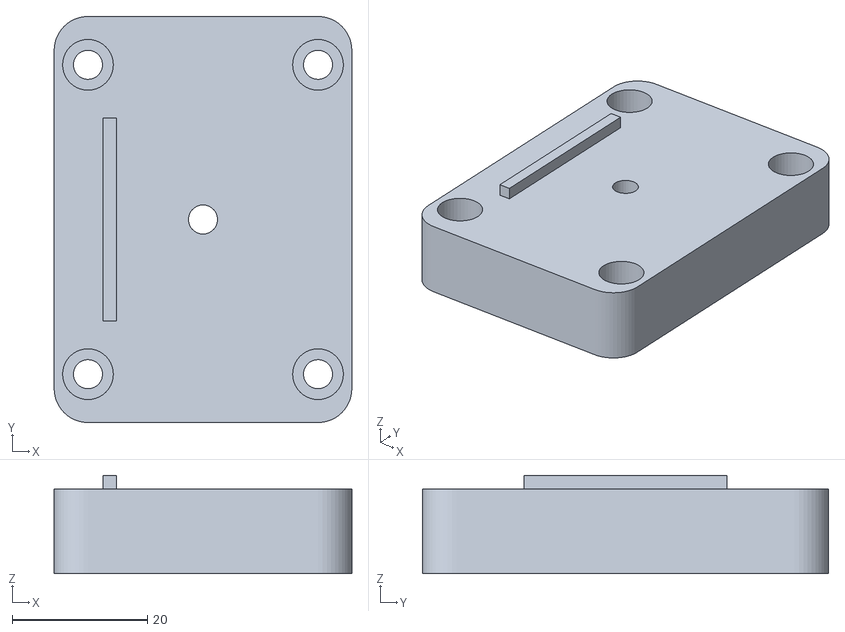
[picture p84: CAD file, 2026-06-10]
stl/shutter_adapter.stl
44.0 x 60.0 x 14.5
