hybrid-lab/PyOpticL_Rubidium_System/stl/Shared-PyOpticL-Folder/SM1FCA2-Step.stl

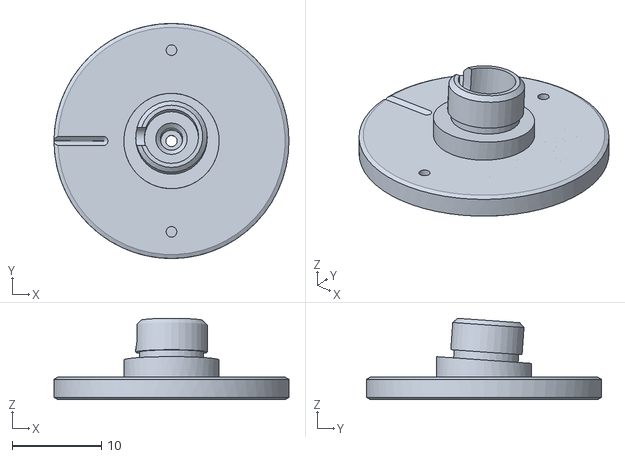
[picture p85: CAD file, 2025-08-15]
stl/Shared-PyOpticL-Folder/SM1FCA2-Step.stl
26.3 x 26.3 x 9.11
