hybrid-lab/PyOpticL_Rubidium_System/stl/SR475.stl

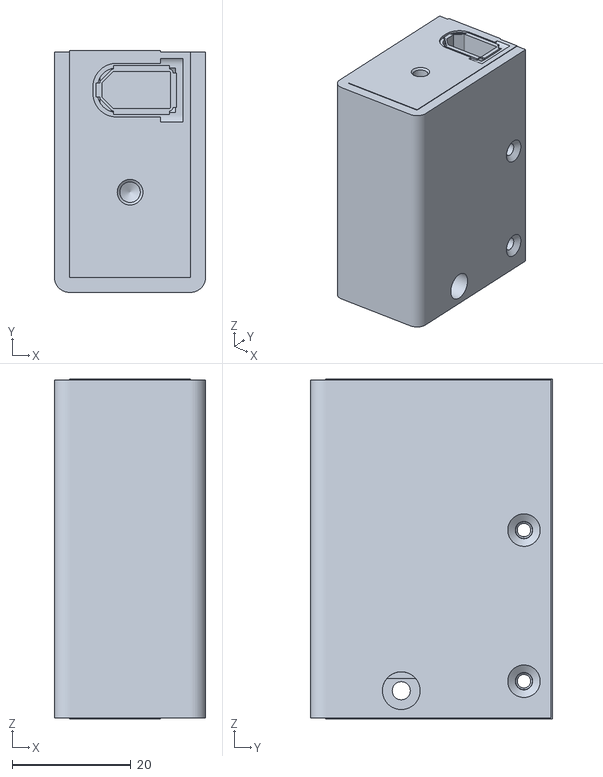
[picture p86: CAD file, 2026-06-10]
stl/SR475.stl
25.4 x 40.6 x 57.2
