hybrid-lab/PyOpticL_Rubidium_System/stl/IOT-5-780-MP.stl

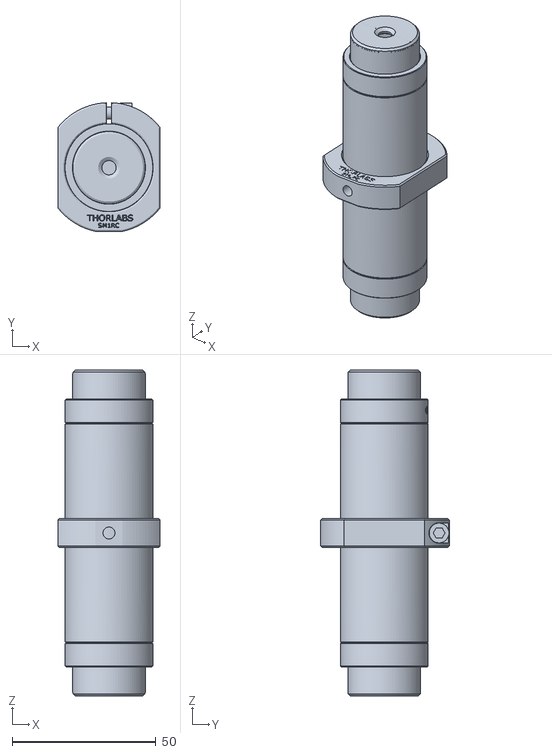
[picture p87: CAD file, 2026-06-10]
stl/IOT-5-780-MP.stl
35.6 x 44.7 x 113.3
