hybrid-lab/PyOpticL_Rubidium_System/stl/Shared-PyOpticL-Folder/BW20M.stl

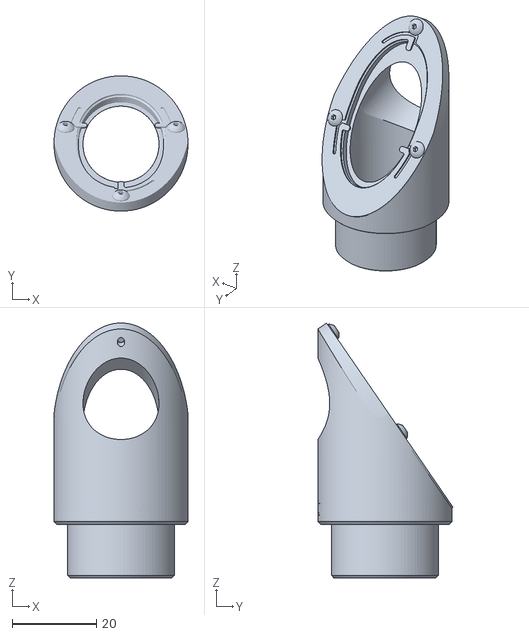
[picture p88: CAD file, 2025-08-15]
stl/Shared-PyOpticL-Folder/BW20M.stl
31.8 x 32.1 x 60.4
