hybrid-lab/PyOpticL_Rubidium_System/stl/PDB250Aa.stl

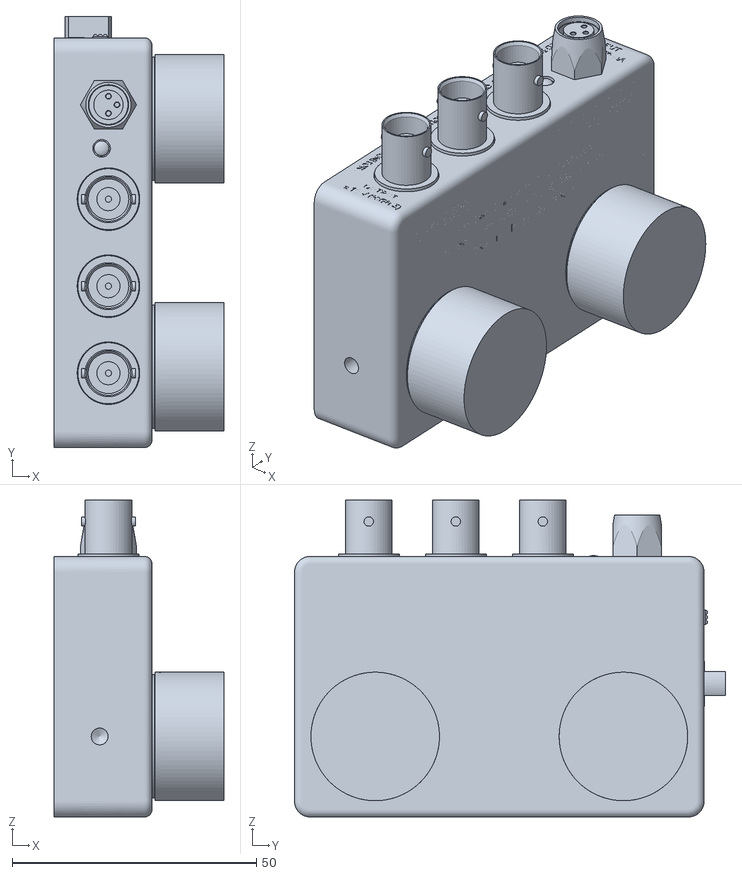
[picture p89: CAD file, 2026-06-10]
stl/PDB250Aa.stl
34.7 x 88.2 x 64.8
