hybrid-lab/PyOpticL_Rubidium_System/stl/Shared-PyOpticL-Folder/rb_cell_holder_base.stl

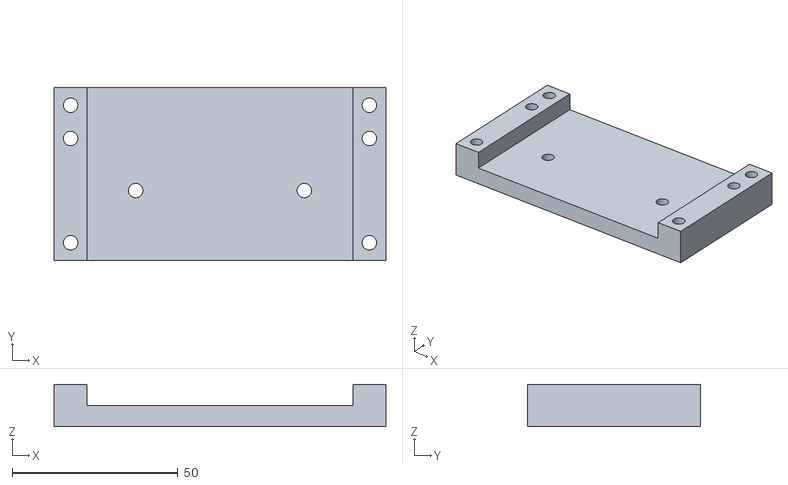
[picture p90: CAD file, 2025-08-15]
stl/Shared-PyOpticL-Folder/rb_cell_holder_base.stl
100.0 x 52.0 x 12.7
