hybrid-lab/PyOpticL_Rubidium_System/stl/DFB_adapter.step

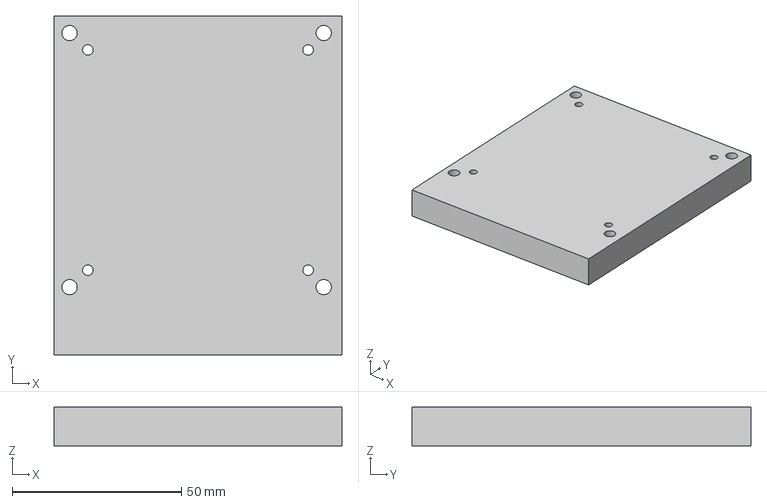
[picture p91: CAD file, 2025-12-15]
stl/DFB_adapter.step
85.0 x 100.0 x 11.4 mm
