hybrid-lab/PyOpticL_Rubidium_System/stl/Shared-PyOpticL-Folder/FMP1-Step.stl

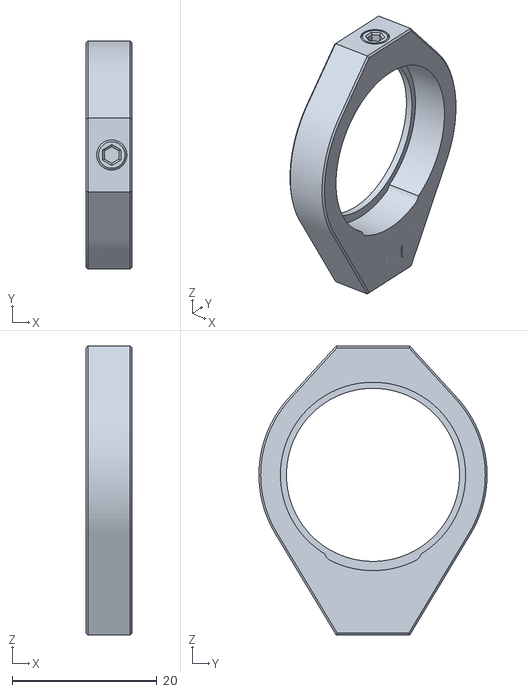
[picture p92: CAD file, 2025-08-15]
stl/Shared-PyOpticL-Folder/FMP1-Step.stl
6.35 x 31.5 x 39.9
