hybrid-lab/PyOpticL_Rubidium_System/stl/Shared-PyOpticL-Folder/SM1L10C_slot_tube.stl

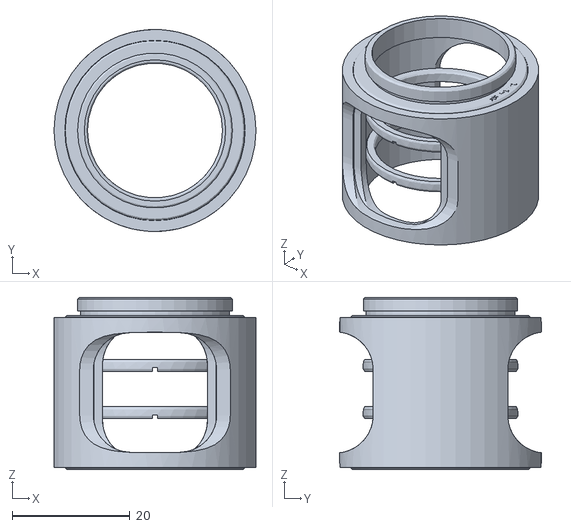
[picture p93: CAD file, 2025-08-15]
stl/Shared-PyOpticL-Folder/SM1L10C_slot_tube.stl
34.3 x 34.2 x 29.2
