hybrid-lab/PyOpticL_Rubidium_System/stl/TA_adapter.stl

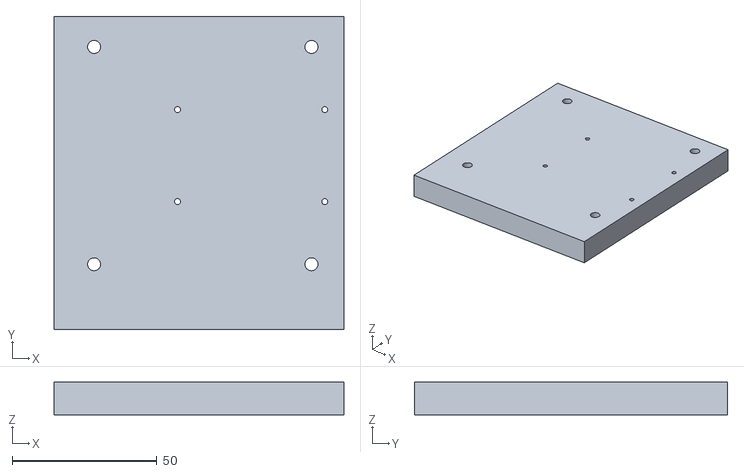
[picture p94: CAD file, 2025-12-15]
stl/TA_adapter.stl
100.0 x 108.0 x 11.3
