hybrid-lab/PyOpticL_Rubidium_System/stl/Shared-PyOpticL-Folder/lens_mount_FMP1.stl

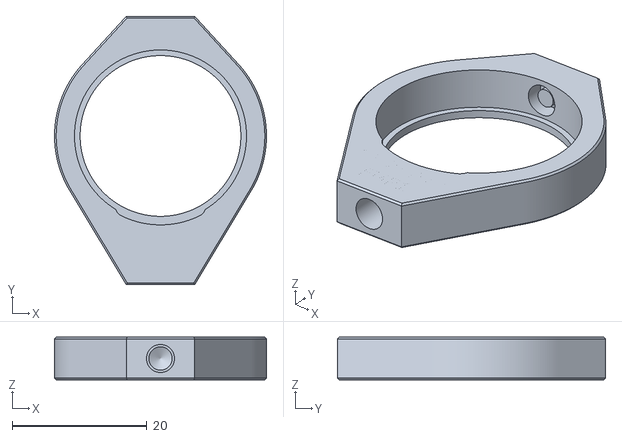
[picture p95: CAD file, 2025-08-15]
stl/Shared-PyOpticL-Folder/lens_mount_FMP1.stl
31.5 x 39.9 x 6.35
