hybrid-lab/PyOpticL_Rubidium_System/stl/Shared-PyOpticL-Folder/small_box__.stl

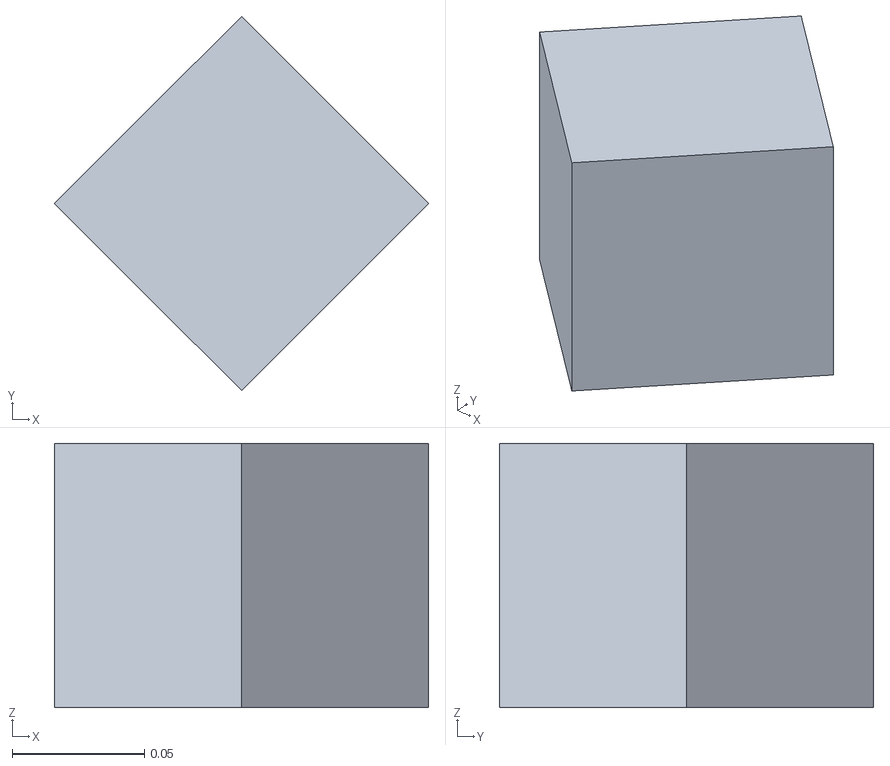
[picture p96: CAD file, 2025-08-15]
stl/Shared-PyOpticL-Folder/small_box__.stl
0.141 x 0.141 x 0.1
