hybrid-lab/PyOpticL_Rubidium_System/stl/koheron-CTL200-V5.step

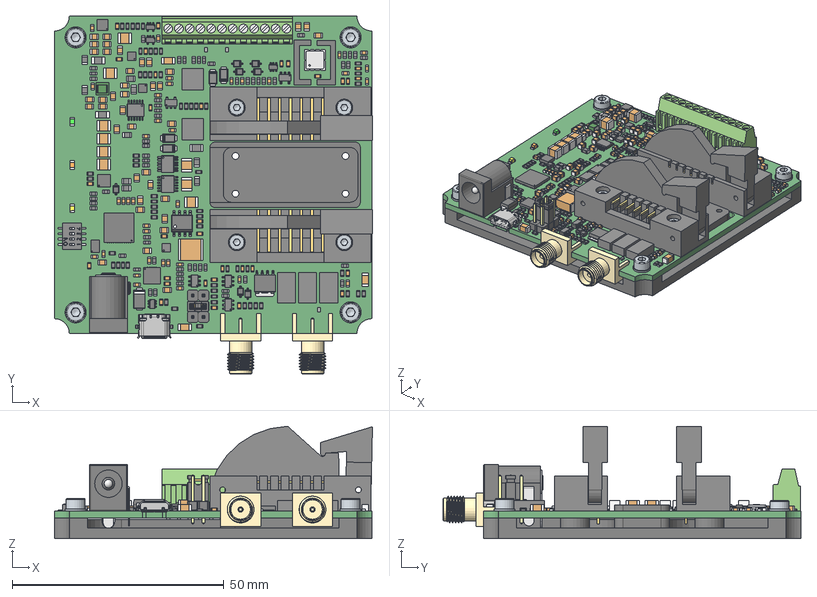
[picture p97: CAD file, 2025-11-09]
stl/koheron-CTL200-V5.step
75.2 x 84.5 x 26.6 mm
CTL200-1
CTL200-1_1
CTL200-1_38
CTL200-1_63
CTL200-1_2
CTL200-1_30
CTL200-1_3
CTL200-1_48
CTL200-1_3_1
CTL200-1_3_2
CTL200-1_60
CTL200-1_25
CTL200-1_91
CTL200-1_37
CTL200-1_64
CTL200-1_4
CTL200-1_34
CTL200-1_1_1
CTL200-1_106
CTL200-1_5
CTL200-1_35
CTL200-1_39
CTL200-1_6
CTL200-1_43
CTL200-1_32
CTL200-1_70
CTL200-1_7
CTL200-1_7_1
CTL200-1_8
CTL200-1_89
CTL200-1_9
CTL200-1_10
CTL200-1_6_1
CTL200-1_50
CTL200-1_15
CTL200-1_62
CTL200-1_11
CTL200-1_54
CTL200-1_12
CTL200-1_58
CTL200-1_24
CTL200-1_1_2
CTL200-1_74
CTL200-1_107
CTL200-1_1_3
CTL200-1_61
CTL200-1_2_1
CTL200-1_59
CTL200-1_2_2
CTL200-1_37_1
CTL200-1_13
CTL200-1_31
CTL200-1_1_4
CTL200-1_1_5
CTL200-1_1_6
CTL200-1_14
CTL200-1_1_7
CTL200-1_108
CTL200-1_54_1
CTL200-1_16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
