hybrid-lab/PyOpticL_Rubidium_System/stl/Shared-PyOpticL-Folder/KM100PM-Step.stl

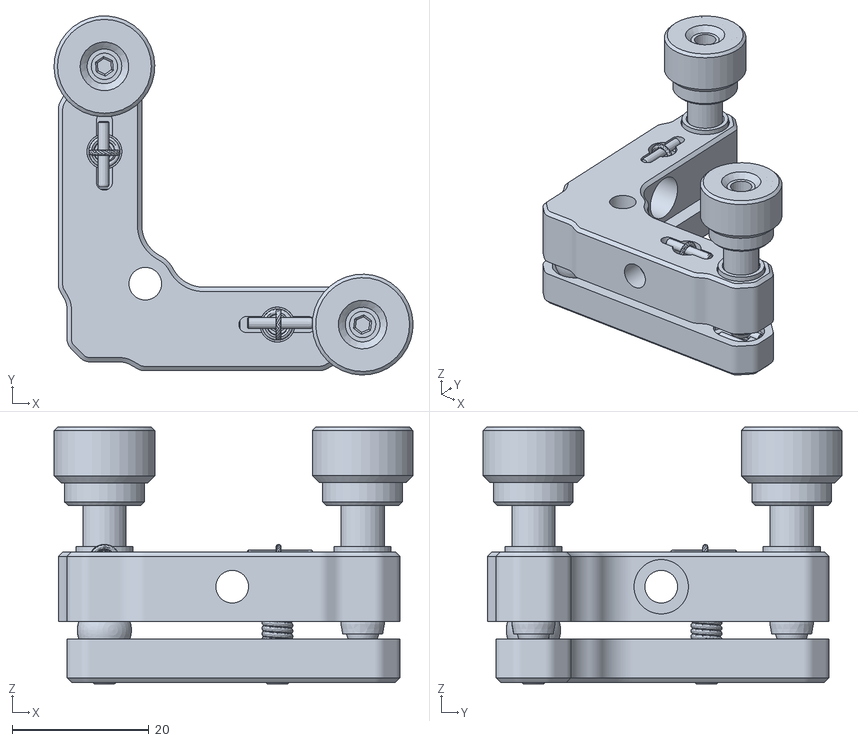
[picture p98: CAD file, 2025-08-15]
stl/Shared-PyOpticL-Folder/KM100PM-Step.stl
52.4 x 52.4 x 37.5
