hybrid-lab/PyOpticL_Rubidium_System/stl/Shared-PyOpticL-Folder/MLH05-Step.stl

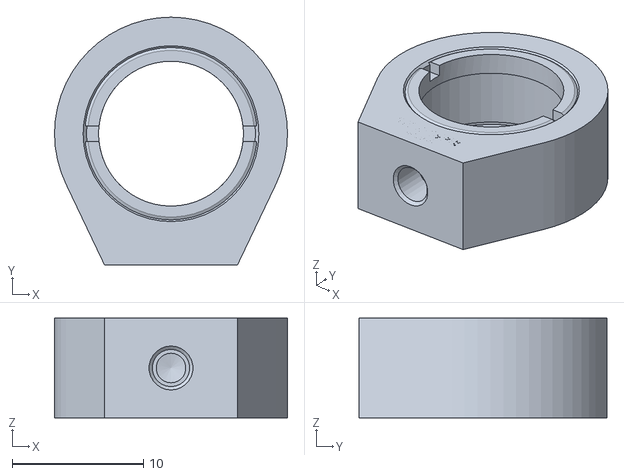
[picture p99: CAD file, 2025-08-15]
stl/Shared-PyOpticL-Folder/MLH05-Step.stl
17.8 x 18.9 x 7.62
