hybrid-lab/PyOpticL_Rubidium_System/stl/koheron_KST25.stl

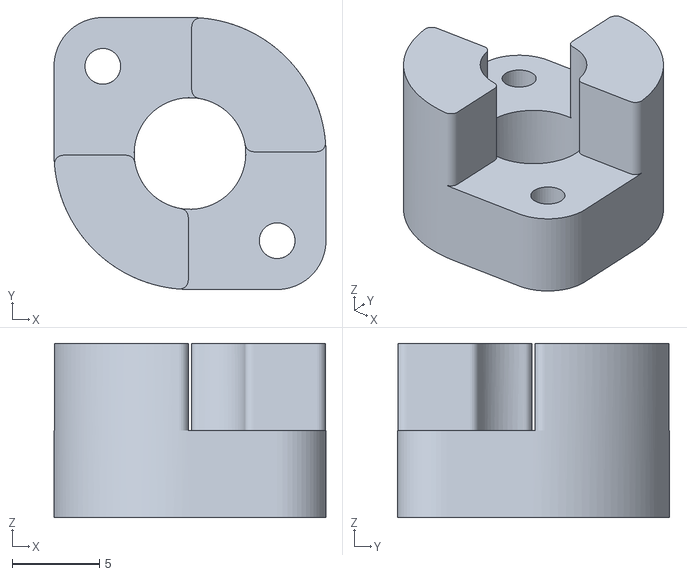
[picture p100: CAD file, 2025-08-15]
stl/koheron_KST25.stl
15.6 x 15.6 x 10.0
