hybrid-lab/PyOpticL_Rubidium_System/stl/Shared-PyOpticL-Folder/wire_tube.stl

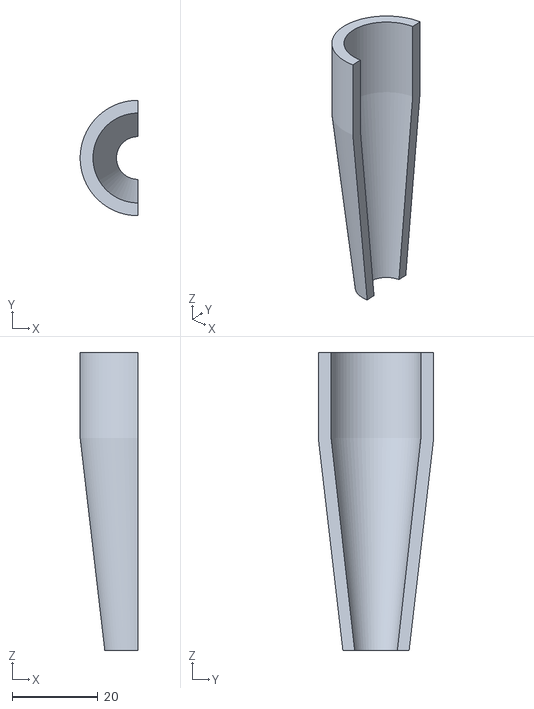
[picture p101: CAD file, 2025-08-15]
stl/Shared-PyOpticL-Folder/wire_tube.stl
13.5 x 27.0 x 69.7
