hybrid-lab/PyOpticL_Rubidium_System/stl/Shared-PyOpticL-Folder/S1TM09-Step.stl

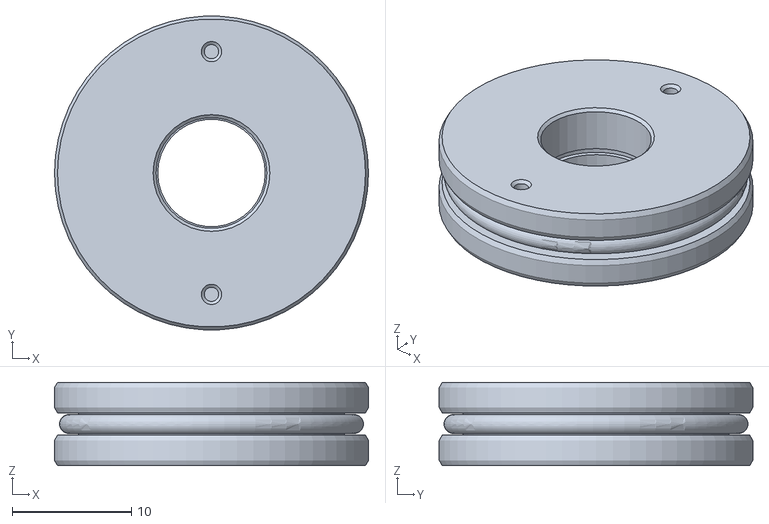
[picture p102: CAD file, 2025-08-15]
stl/Shared-PyOpticL-Folder/S1TM09-Step.stl
26.3 x 26.3 x 6.99
