hybrid-lab/PyOpticL_Rubidium_System/stl/Shared-PyOpticL-Folder/HKTS-5_64-Step.stl

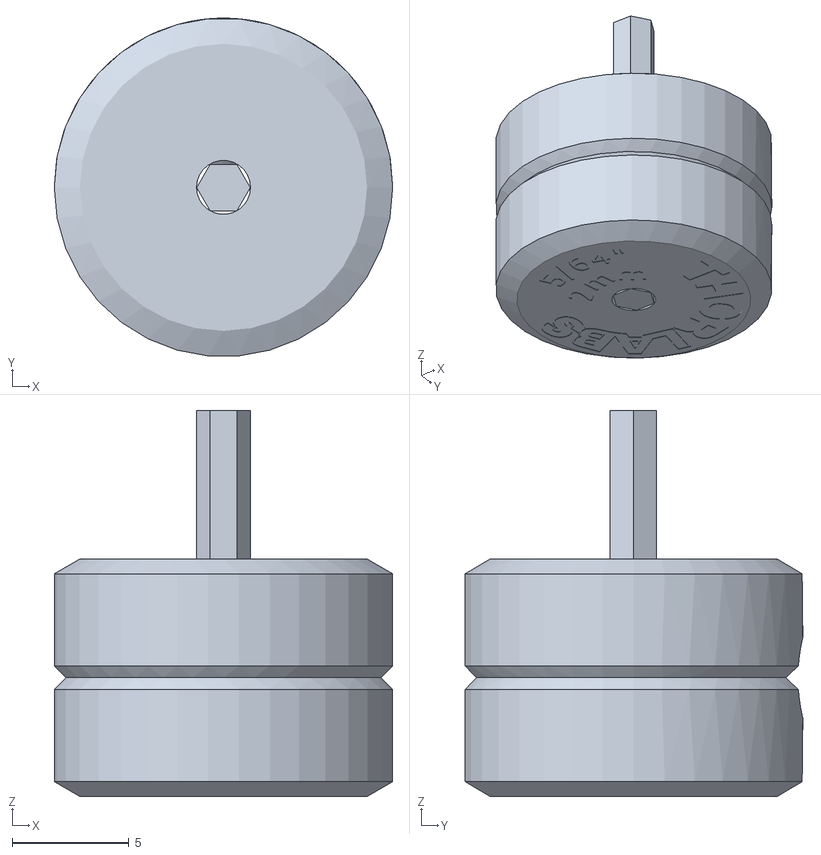
[picture p103: CAD file, 2025-08-15]
stl/Shared-PyOpticL-Folder/HKTS-5_64-Step.stl
14.5 x 14.4 x 16.5
