hybrid-lab/PyOpticL_Rubidium_System/stl/VBC2.stl

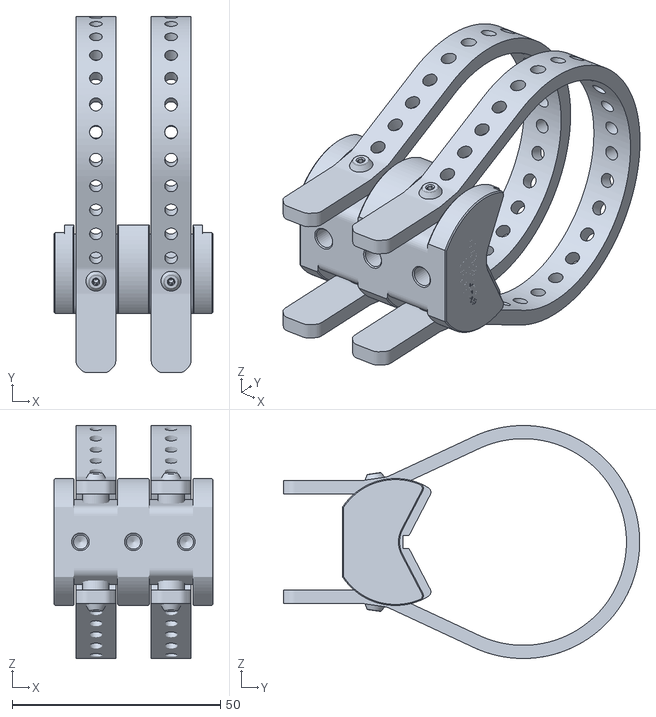
[picture p104: CAD file, 2025-08-15]
stl/VBC2.stl
38.1 x 85.5 x 55.9
