hybrid-lab/PyOpticL_Rubidium_System/stl/Shared-PyOpticL-Folder/TEC.stl

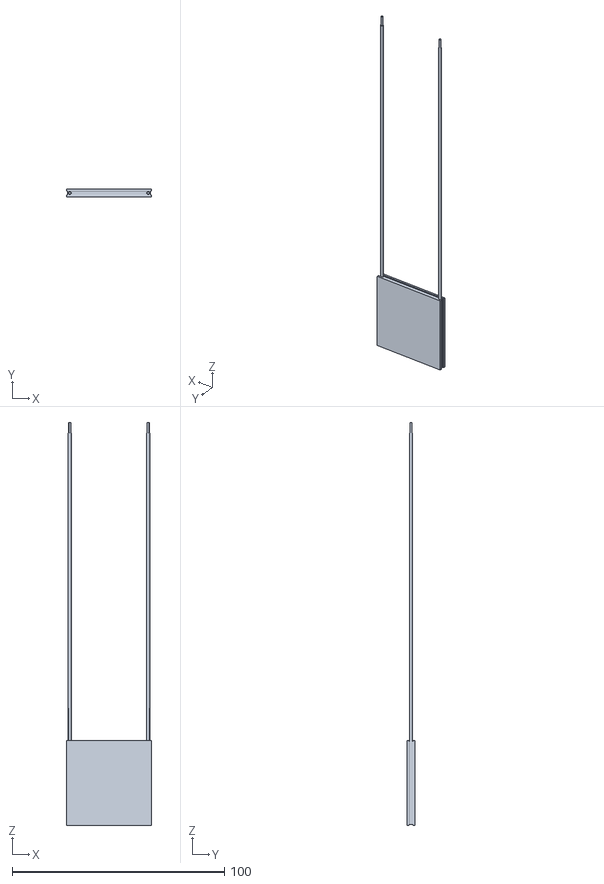
[picture p106: CAD file, 2025-08-15]
stl/Shared-PyOpticL-Folder/TEC.stl
40.0 x 3.80 x 190.0
