hybrid-lab/PyOpticL_Rubidium_System/stl/Shared-PyOpticL-Folder/SM1L05-Step.stl

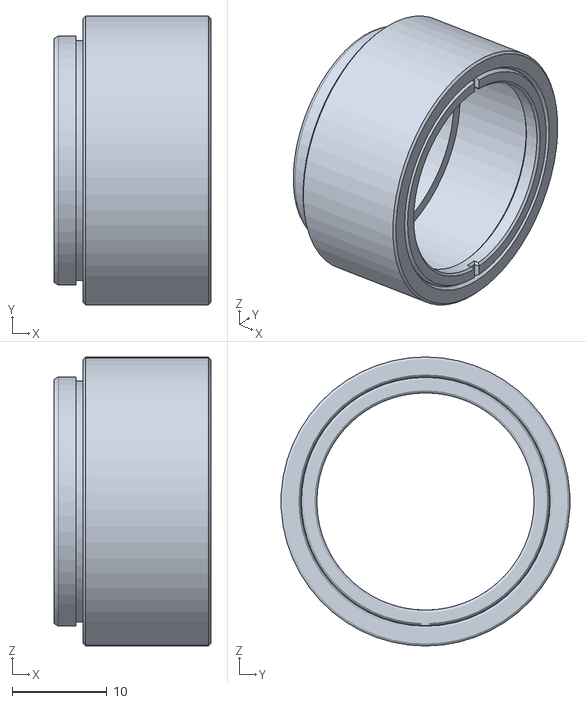
[picture p107: CAD file, 2025-08-15]
stl/Shared-PyOpticL-Folder/SM1L05-Step.stl
16.5 x 30.4 x 30.5
