hybrid-lab/PyOpticL_Rubidium_System/stl/IOT-5-850-VLP-Step.stl

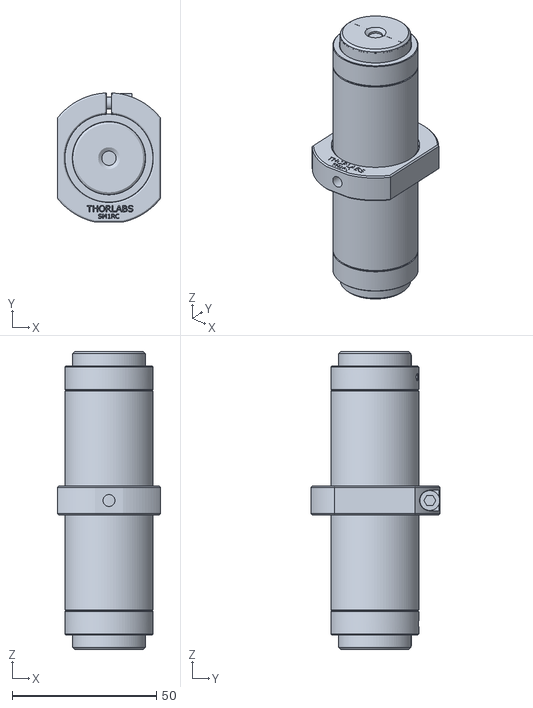
[picture p108: CAD file, 2025-08-15]
stl/IOT-5-850-VLP-Step.stl
35.6 x 44.7 x 103.1
