hybrid-lab/PyOpticL_Rubidium_System/stl/Shared-PyOpticL-Folder/SMR05-Step.stl

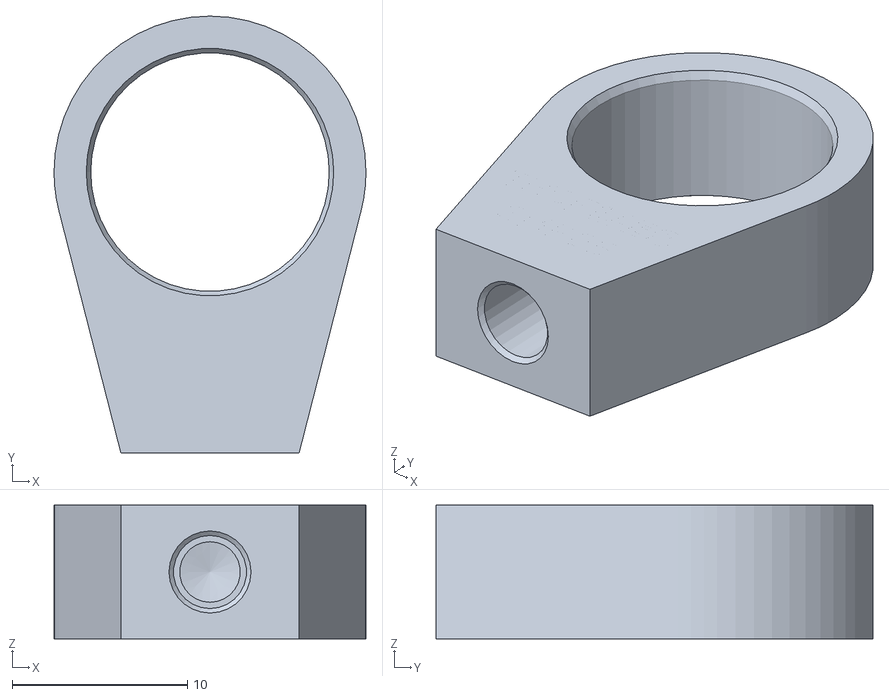
[picture p109: CAD file, 2025-08-15]
stl/Shared-PyOpticL-Folder/SMR05-Step.stl
17.8 x 24.9 x 7.62
