hybrid-lab/PyOpticL_Rubidium_System/stl/KM05T-Solidworks.sldprt

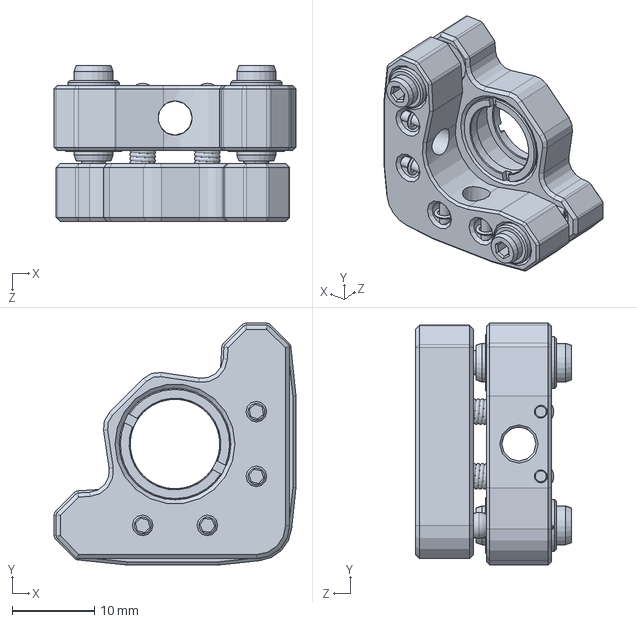
[picture p110: CAD file, 2025-08-15]
stl/KM05T-Solidworks.sldprt
29.5 x 29.5 x 19.1 mm
