hybrid-lab/PyOpticL_Rubidium_System/stl/Shared-PyOpticL-Folder/isomet_1205c.stl

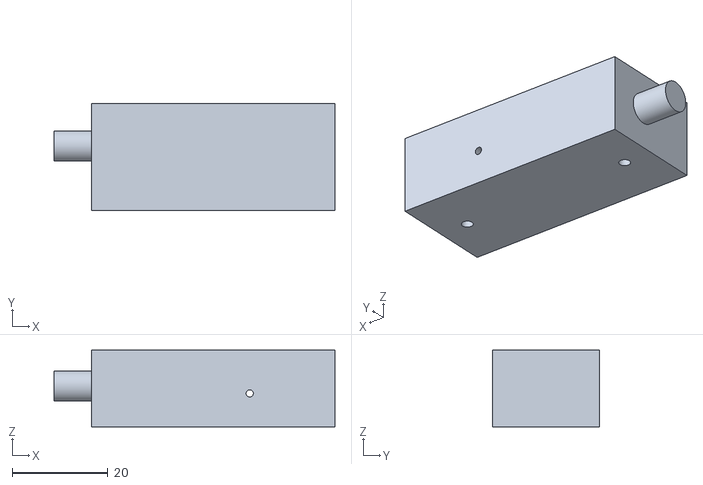
[picture p111: CAD file, 2025-08-15]
stl/Shared-PyOpticL-Folder/isomet_1205c.stl
58.6 x 22.3 x 16.0
