hybrid-lab/PyOpticL_Rubidium_System/stl/Shared-PyOpticL-Folder/S05LM56-Step.stl

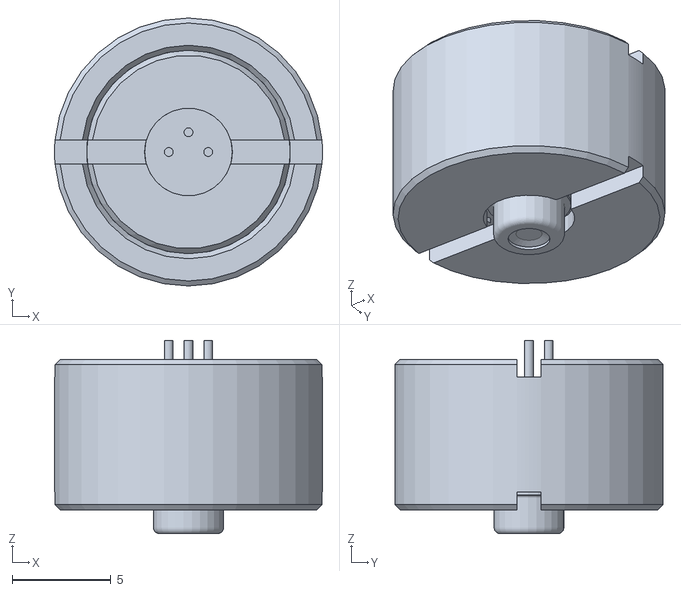
[picture p112: CAD file, 2025-08-15]
stl/Shared-PyOpticL-Folder/S05LM56-Step.stl
13.6 x 13.6 x 9.80
