hybrid-lab/PyOpticL_Rubidium_System/stl/aomo_3100-125.stl

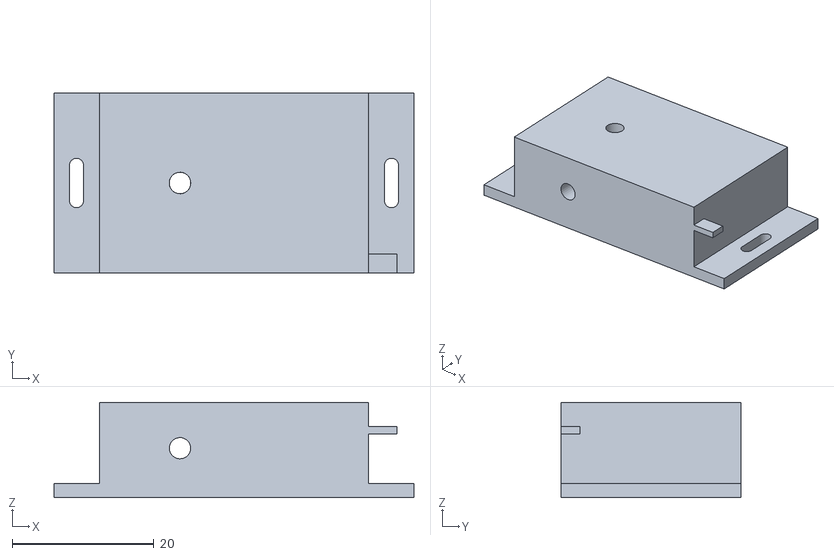
[picture p113: CAD file, 2025-08-15]
stl/aomo_3100-125.stl
50.8 x 25.4 x 13.5
