hybrid-lab/PyOpticL_Rubidium_System/stl/Shared-PyOpticL-Folder/SM05FCA2-Step.stl

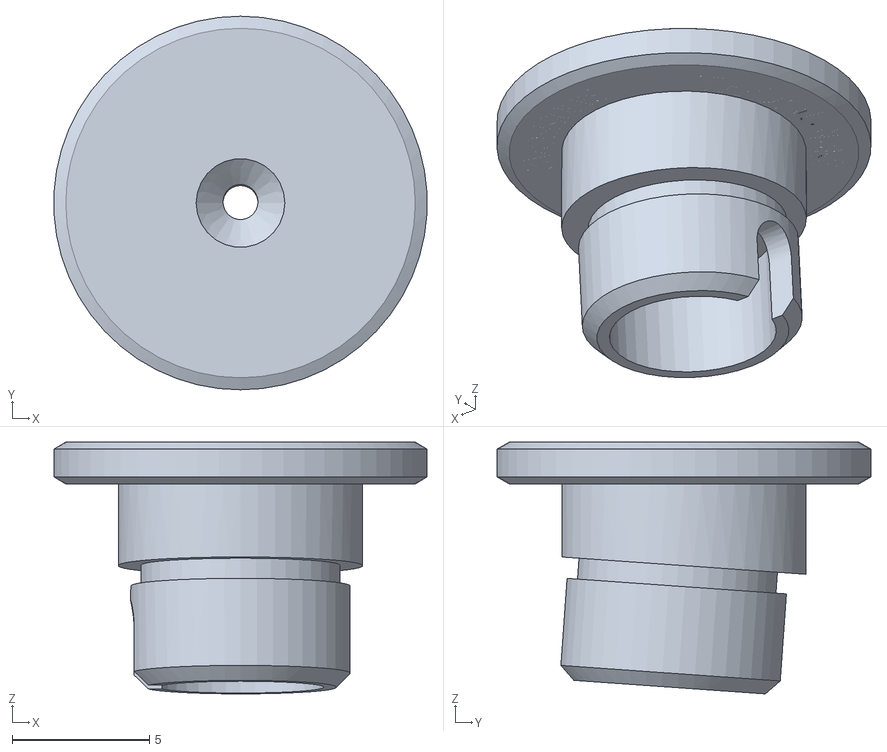
[picture p114: CAD file, 2025-08-15]
stl/Shared-PyOpticL-Folder/SM05FCA2-Step.stl
13.6 x 13.6 x 9.16
