hybrid-lab/PyOpticL_Rubidium_System/stl/Shared-PyOpticL-Folder/RSP05-Step.stl

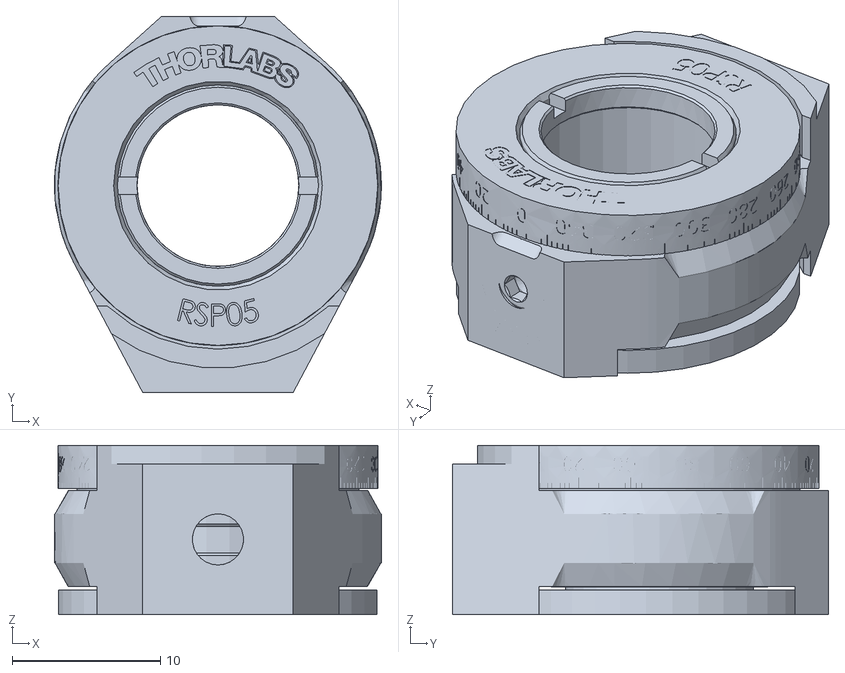
[picture p115: CAD file, 2025-08-15]
stl/Shared-PyOpticL-Folder/RSP05-Step.stl
22.1 x 25.4 x 11.4
