hybrid-lab/PyOpticL_Rubidium_System/stl/Shared-PyOpticL-Folder/SM1TC-Step.stl

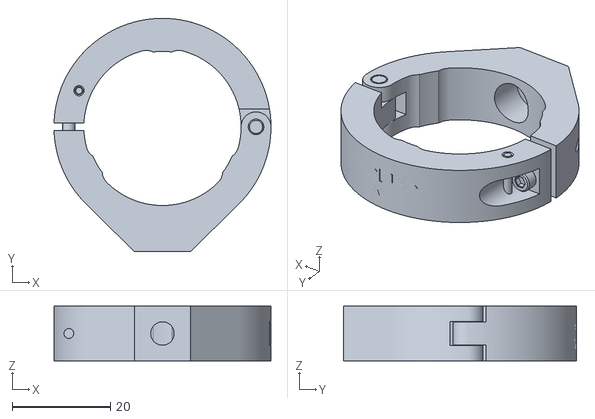
[picture p116: CAD file, 2025-08-15]
stl/Shared-PyOpticL-Folder/SM1TC-Step.stl
44.2 x 47.5 x 11.2
