hybrid-lab/PyOpticL_Rubidium_System/stl/IO-3D-780-VLP-Step.stl

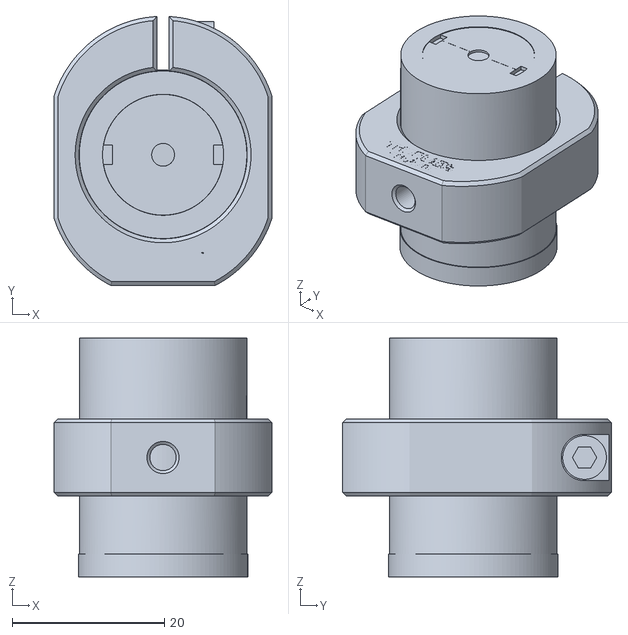
[picture p117: CAD file, 2025-08-15]
stl/IO-3D-780-VLP-Step.stl
28.6 x 35.3 x 31.3
