hybrid-lab/PyOpticL_Rubidium_System/stl/Shared-PyOpticL-Folder/Fiberport_mount_k1t1.stl

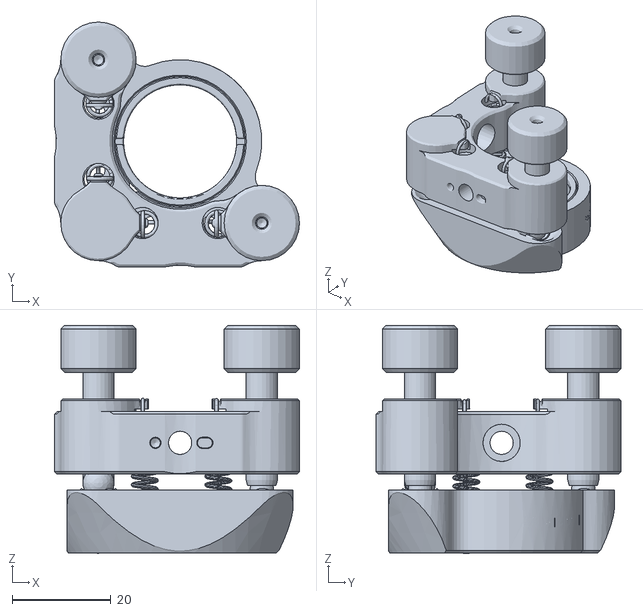
[picture p118: CAD file, 2025-08-15]
stl/Shared-PyOpticL-Folder/Fiberport_mount_k1t1.stl
49.5 x 49.5 x 46.2
