hybrid-lab/PyOpticL_Rubidium_System/Production/TABoard/Drawing/Cube_Mount_Halfinch Drawing.pdf

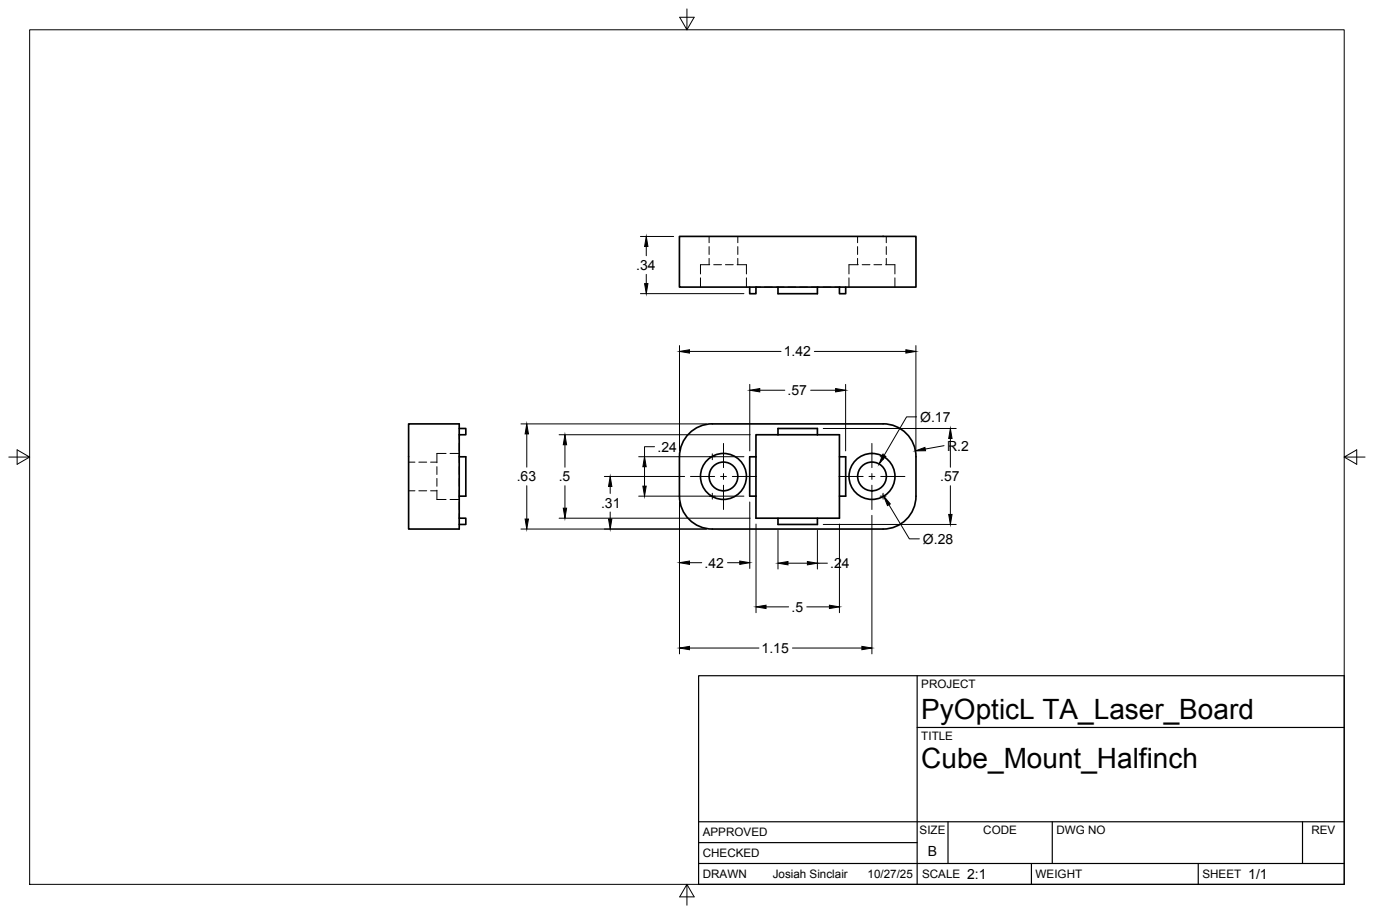
[picture p129: page 1]
SIZE; CODE; DWG NO; REV; Josiah Sinclair; PyOpticL TA_Laser_Board
