hybrid-lab/PyOpticL_Rubidium_System/Production/TABoard/Drawing/TA_adapter Drawing.pdf

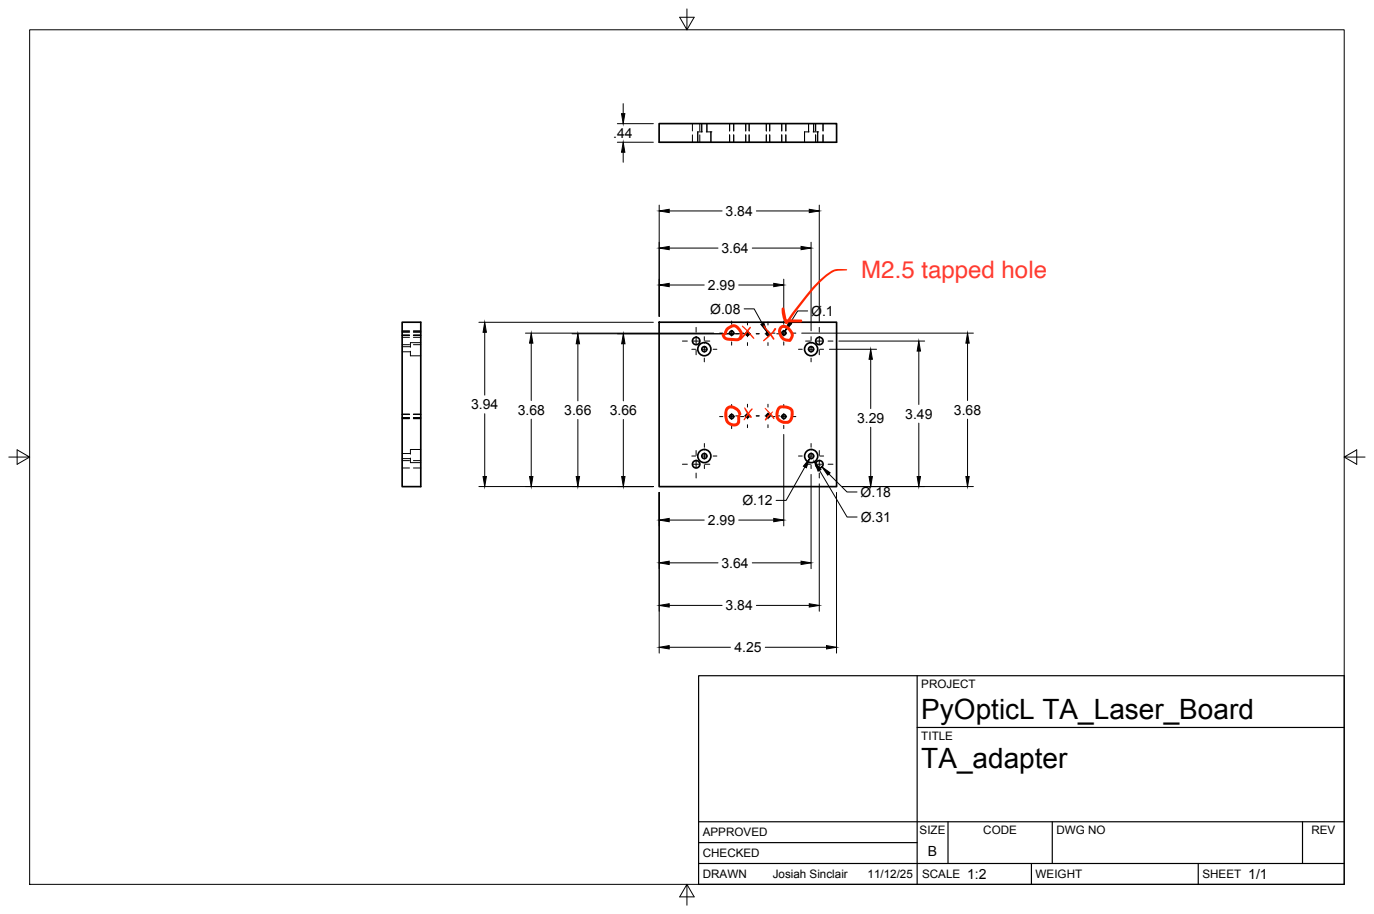
[picture p130: page 1]
SIZE; CODE; DWG NO; REV; Josiah Sinclair; PyOpticL TA_Laser_Board
