hybrid-lab/PyOpticL_Rubidium_System/Production/TABoard/Drawing/TA_Laser-Baseplate Drawing CORRECT.pdf

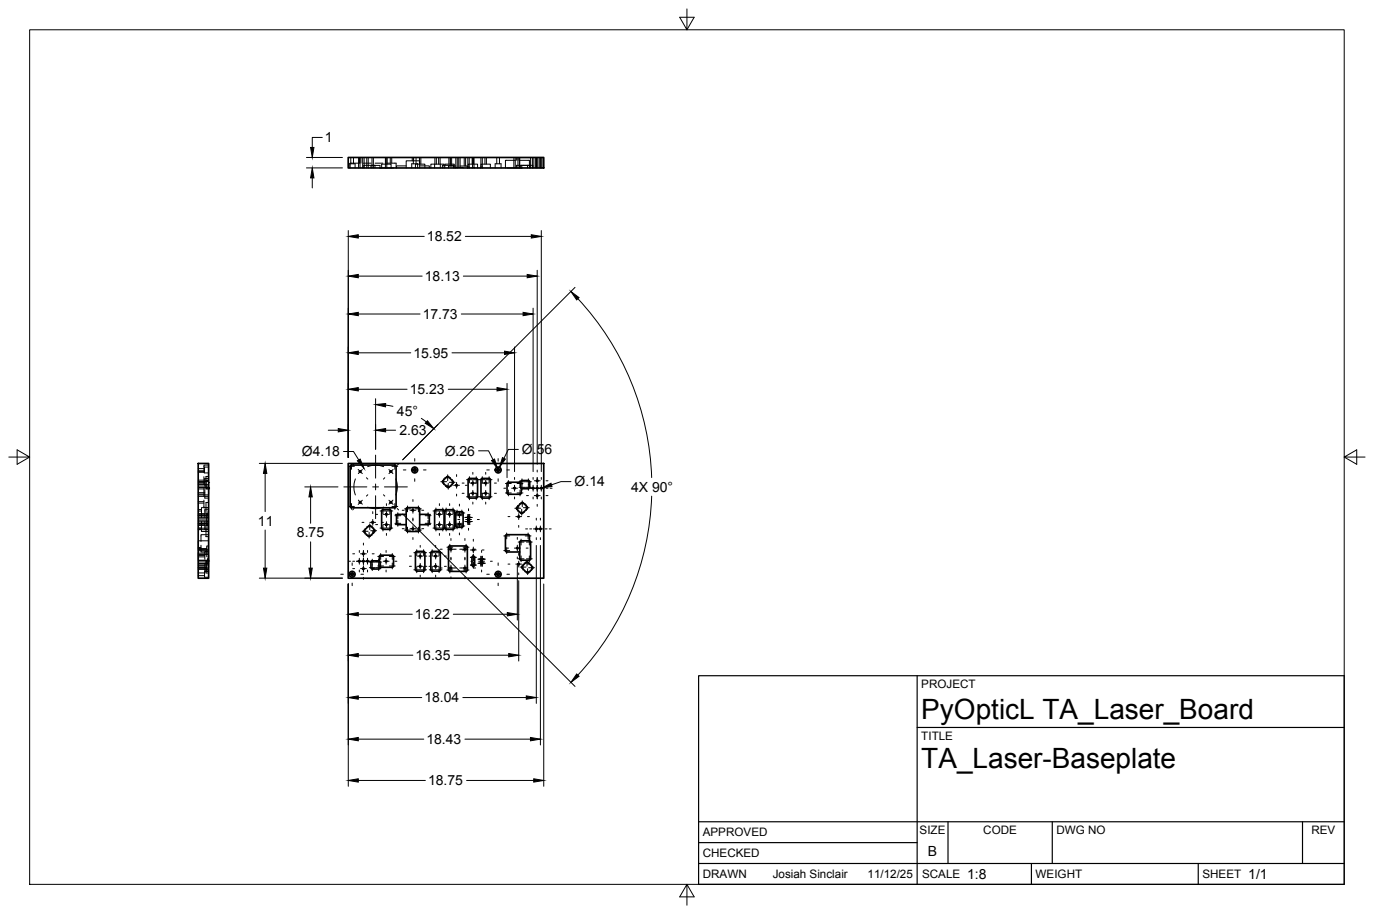
[picture p131: page 1]
SIZE; CODE; DWG NO; REV; Josiah Sinclair; PyOpticL TA_Laser_Board
