hybrid-lab/PyOpticL_Rubidium_System/Production/Adapters/Drawing/Cube_Mount.pdf

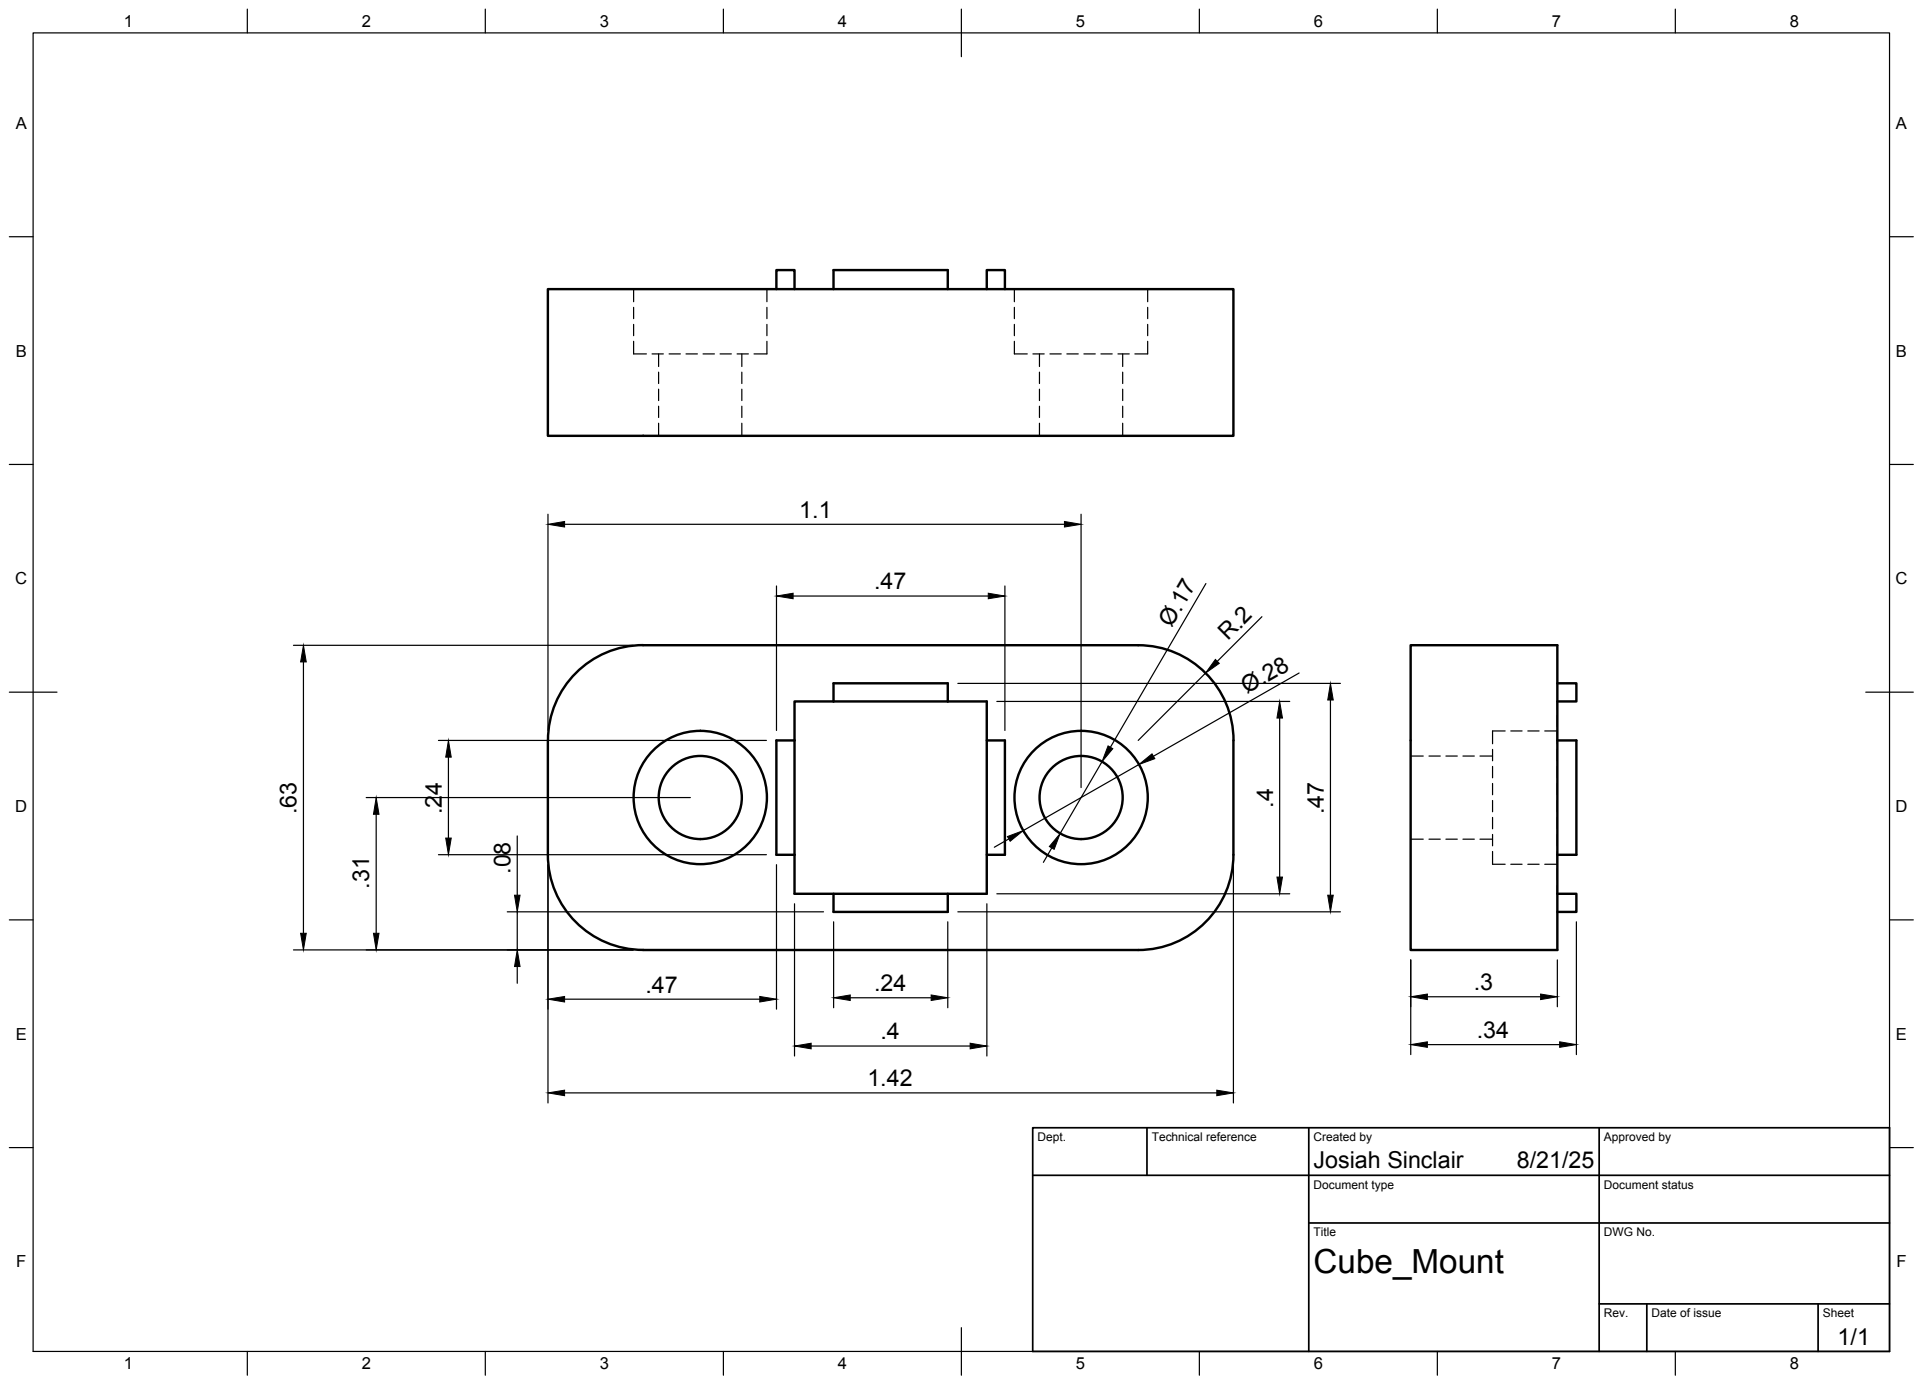
[picture p132: page 1]
Title; DWG No.; Rev.; Date of issue; Sheet

Dept. | Technical reference | Created by Josiah Sinclair 8/21/25 | Approved by

Document type | Document status
