hybrid-lab/PyOpticL_Rubidium_System/Production/Adapters/Drawing/Surface_Adapter_fiberport_lip.pdf

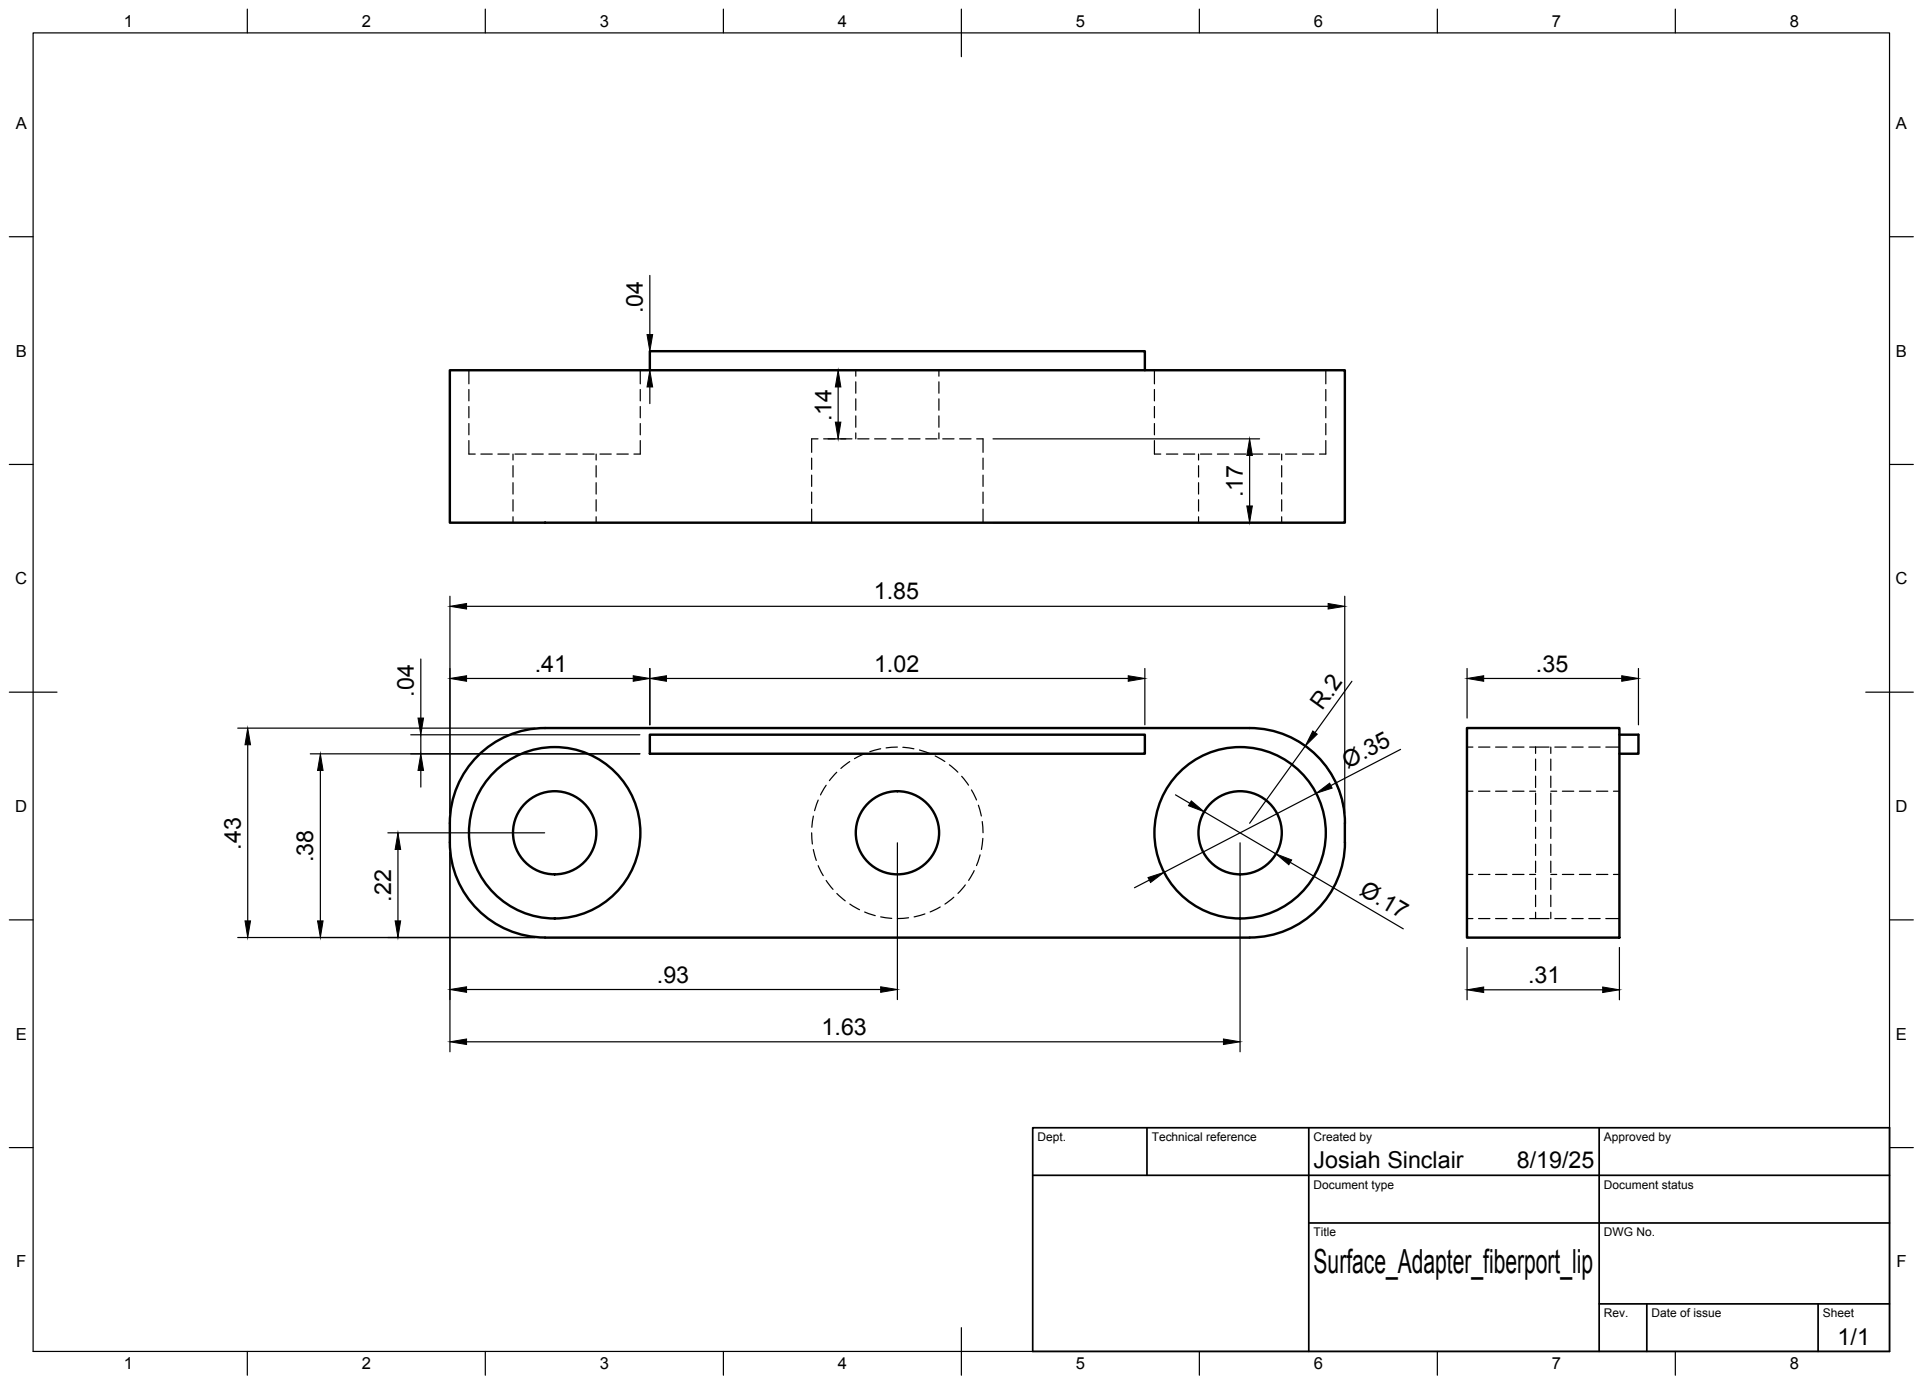
[picture p133: page 1]
Title; DWG No.; Rev.; Date of issue; Sheet

Dept. | Technical reference | Created by Josiah Sinclair 8/19/25 | Approved by

Document type | Document status
